nova-rey/pisxme/pisxme/reva-clean/PHASE19_BLOCKER_REPORT.md

# Phase 19 SATA routing blocker (active, non-terminal)

## 2026-09-05 orthogonal coordinated-generator sweep

A direct-generator class evaluated U7 rotation 180 with explicit orthogonal
J3 launches at `(140,110)/(180,95)`, `(170,110)/(230,95)`, and
`(190,100)/(250,95)`. Native DRC measured `434`, `377`, and `416` violations;
each retained `413` unconnected items and `17`, `21`, and `24` crossing/short
records. Coordinate-only movement does not repair the stale route construction.
The next implementation must replace the bridge/socket route topology from
live pad coordinates while co-generating the clock network. No sweep candidate
is promoted.

## 2026-09-05 live U7 rotation-180 clock transform correction

The clock authoring path previously used the old synthetic U7 origin even when
applied to `PHASE19_COORDINATED_PASS_CANDIDATE_FINAL` (`U7` at `(120,140)`,
rotation 180). The generic fixture now reflects its passing local graph about
the live U7 center and supports a parameterized support shift. The generated
clock support is at the expected transformed locations (`Y1` `(120,125)`
before shift), and the three U7 clock routes land on serialized pads
`52=(123,135.5)`, `53=(122.5,135.5)`, and `54=(122,135.5)`.

The corrected no-shift candidate was rejected at 234 native DRC violations /
413 unconnected items, with new records where the correctly landed clock
routes occupy the inherited SATA corridor. A west-shifted run reduced the
clock-related crossing/short class to 10 records but still collided with
live SATA and regulator geometry. This closes the stale-coordinate hypothesis
and identifies the next required class: regenerate U7/J3/clock together with
the clock support outside the live SATA corridor.

The corrected live-U7 transform was swept with support shifts `-5, -10, -15,
-20, -25, -30, -35, -40 mm` on the best no-crossing coordinated ancestor.
The best result was the `-20 mm` shift at 245 native DRC violations / 417
unconnected items, with 9 crossing/short records; the other shifts were no
better. This bounded negative result confirms that moving clock support within
the existing U7/J3 placement cannot clear SATA occupancy. The next credible
step is one regenerated storage island with a dedicated clock corridor.

An outboard coordinated storage-room experiment moved U7 to `(180,140)` and
J3 to `(250,100)` while retaining the V3 SATA authoring branch, then applied
the corrected live-U7 clock transform with a `-20 mm` support shift. Native
DRC reported `417` unconnected items and 29 crossing/short records. The
candidate is rejected: the outboard J3 move alone does not repair the stale
USB3/SATA route construction or provide a valid integrated clock corridor.
No PCIe or architecture change was made.

An occupancy-aware routing experiment was then added as a bounded diagnostic.
It derives the live U7 clock pads, places the oscillator island in open
acreage, and routes each clock net on B.Cu while treating inherited copper and
previously emitted nets as obstacles. The source-to-crystal search exposes a
closed inherited B.Cu corridor at the proposed support field before a complete
passive branch can be emitted. The experiment is retained as rejected
evidence; it does not weaken the layer contract or validate a partial clock
network. The next credible implementation must move the complete U7/J3
storage island, not just the support footprints, so the clock and SATA
corridors are planned together.

## 2026-09-04 local underside clock-island follow-up

The next authorized class was implemented as a parameterized authoring path in
`phase19_clock_local_bcu.py`. It keeps the authoritative U7 XI/VSSOSC/XO
escape perpendicular at the live rot270 pad row, transitions with ordinary
through-vias, and places the low-profile Y1/R23/C42/C43 support island on
B.Cu. This removes the earlier F.Cu clock trunk through the inherited USB3
and low-speed corridors.

The first corrected run exposed two further facts. The inherited coordinated
candidate contains substantial pre-existing connectivity/clearance debt, and
the underside support graph must be routed as a planar perimeter rather than
as a three-net star. The near-support run (`Y1` at `(145,125)`) measured 365
native DRC violations / 429 unconnected items and still has clock-local
XI/XO/VSSOSC crossings at the support field. A south-acreage run (`Y1` at
`(140,160)`) measured 366 / 429 and has the same local support-field class.
The experiments are rejected; no Phase 19 gate is claimed closed.

The U7-side failure is now correctly separated from the previous error: the
first version routed vertically through adjacent no-connect QFN pads 50/51;
the generic path was corrected to leave the 0.5 mm pitch row laterally first.
The remaining blocker is the support-island topology and available copper
corridor, not a missing TUSB9261 clock authority. The passing isolated clock
fixture remains the electrical reference. PCIe, USB3/SATA architecture,
stack, and Phase 18 ancestor are unchanged.

The required independent Consultant unblocker review was invoked with the
current Phase 18 ancestor, Phase 19 report, exact U7/J3 coordinates, and the
failed underside trials. The session exceeded the bounded response window
and was cancelled; this is recorded as orchestration latency, not evidence of
an engineering hard block. The selected continuation remains in-scope:
author a planar oscillator perimeter with explicit live pad coordinates,
co-locate it during the rotated U7/J3 generation, and validate the clock delta
against the SATA-only ancestor before any promotion.

A second placement sweep moved the underside support island to upper-right and
lower-edge acreage (`Y1` at `(200,100)`, `(220,100)`, `(250,90)`, and
`(260,160)`). Native DRC remained in the `364--375` violation range with
`429` unconnected items; clock-local support-field crossings/shorts remained,
and some placements additionally intersected inherited CM5/PCIe/connector
copper. No placement was promoted. The next authoring change must use the
known passing isolated-clock graph as the local support template and
regenerate its three U7 source corridors together, rather than applying
another support-coordinate-only overlay.

The coordinated generator was also exercised directly at U7/J3 placements
`(150,100)/(230,100)`, `(180,90)/(250,105)`, and `(200,80)/(270,100)` with
the authoritative V3 SATA branch and U7 rotation 180. Native DRC measured
`426`, `473`, and `364` violations respectively, with `413` unconnected
items in each artifact and `13`, `20`, and `24` crossing/short records. These
are rejected as placement sweep evidence: the lower raw DRC count does not
pass because the coordinated USB3/SATA connectivity gate remains open, and
the clock network still has to be generated and routed as part of the same
candidate.

## 2026-09-04 coordinated storage authoring repair

The coordinated-island generator was corrected after a KiCad 10 serialization
audit. The Phase 18 donor reuses C30-C33 for unrelated regulator capacitors;
the generator now removes those donor footprints and loads the project-local
0402 footprints. It also assigns explicit net codes and attaches the new
socket-side nets before synchronization reload, preserving the intended
C30-C33/J3 split mapping.

Disposable candidate U7 `(150,140)` / J3 `(180,125)` completed generation and
serialized the expected four SATA socket nets, but native DRC measured 262
violations. Candidate-introduced SATA launch crossings/shorts and inherited
CM5/PERST interactions remain, so this candidate is rejected. Evidence is in
`PHASE19_COORDINATED_STORAGE_REPAIR_RECEIPT.md`; Phase 19 remains active and
no Phase 20+ work has started.

Follow-up USB3 escape refinement reduced the USB-only V3 disposable report to
200 native DRC violations by approaching the moved U7 row horizontally, but
it still crosses inherited CM5/PCIe source-corridor geometry and is rejected.
This remains a coordinated storage-island routing experiment, not a Phase 19
closure claim.

The best current coordinated V3 run (`PHASE19_BEST.kicad_pcb`, U7 `(120,140)`
180 degrees, J3 `(145,125)` 90 degrees) measured 206 native DRC violations.
It retains one J3 auxiliary-pad short and two USB3/PCIe or local corridor
crossings, so it is rejected. The cap-net serialization failures remain fixed.

The refined synchronized candidate `PHASE19_LIVE3.kicad_pcb` is the current
best local result: native DRC measured 207 violations with zero shorting-item
records and one remaining USB3 source/landing crossing. It also retains
inherited clearance/hole/unconnected debt, so Phase 19 remains open and the
candidate is rejected.

Date: 2026-09-04

Status: `PISXME_REVA_CLEAN_PHASE19_SATA_ROUTING_IN_PROGRESS`

## 2026-09-04 coordinated-island continuation

The authoring harness was corrected so C30-C33 follow the requested U7
coordinate instead of retaining the former fixed x positions. A second
correction adds an opt-in direct USB3 landing mode for the validated
Phase-18 U7 neighborhood. With U7 `(110,105)` and USB3-only generation,
native DRC reports zero USB3 `tracks_crossing` and zero USB3 `shorting_items`;
the one remaining crossing/short category is inherited CM5/PERST or frozen
PCIe geometry outside the USB3 island.

The first complete orthogonal SATA launch experiment at U7 `(110,105)` and
J3 `(150,110)` rotation 0 was rejected. Native DRC identified concrete local
failures: RX_N crossing the frozen PCIe B.Cu corridor, connector-pad launch
shorts caused by the trial's J3 approach points, and one RX via near an
existing power-input pad. This is evidence against that exact trial, not
against the CM5-to-SATA architecture. No PCIe or Phase-18 ancestor copper was
modified.

The active blocker therefore remains a recoverable coordinated storage-island
placement/routing problem. The next bounded experiment must move the complete
island into genuinely open acreage or adjust the J3 orientation/edge while
retaining the direct USB3 landing mode, then derive all SATA launch points
from the actual connector pad and courtyard geometry. Phase 19 remains open;
Phase 20+ has not started.

## Independent high-speed review and V3-cap continuation

An independent PCB review confirmed the prior crossing diagnosis: the named
`(95,140)` marker is the RX_N landing segment, and its actual conflict is the
F.Cu TX_N diagonal, not TX_P. The review also identified that the direct
RX_N patch must account for the adjacent U7 pad field and that the live
candidate is not SI-closed until length/skew and transition-return evidence
are measured.

The generator now has an opt-in `P19_RXN_DIRECT` branch that preserves the
source corridor and uses a short ordinary-via return beside the serialized
RX_N pad. A V3-cap candidate using U7 `(120,140)` rotation 180 and J3
`(145,125)` rotation 90, with C30-C33 placed inline in the proven V3 lanes,
was generated and reloaded by KiCad 10. Native DRC measured 316 total
violations, zero `shorting_items`, and one `tracks_crossing`. The sole
crossing is RX_N on B.Cu against the frozen PCIe B.Cu trunk; SATA itself has
zero crossing/short records in this candidate. It is therefore rejected but
is the best current decomposition of the remaining problem.

The next experiment must move that one RX_N transition off the PCIe trunk or
select a nearby U7/J3 placement with the same V3 SATA lane ordering. It must
also include the independent review's required USB3 pair-length/skew audit
and local GND return-via review. A separate review noted U7 clock pads 52/53
remain unassigned in the current inherited materialization; this is retained
as a Phase 7/19 authority item and is not silently waived.

## 2026-09-04 coordinated repath baseline

The coordinated USB3 repath was extended across all four branches while
retaining the V3 split-cap SATA geometry. The generated/reloaded candidate is
`PHASE19_COORDINATED_PASS_CANDIDATE3.kicad_pcb` with U7 `(120,140)` rotation
180 and J3 `(145,125)` rotation 90. Native DRC reports 189 total violations,
418 unconnected items, zero `tracks_crossing`, zero `shorting_items`, and the
three inherited clearance plus two inherited hole-clearance records, with the
same five inherited dangling-via records as the accepted Phase-18 acreage
baseline. No candidate-introduced true clearance, short, or crossing remains
in the high-speed routing categories.

The candidate also removes the inherited duplicate U7 pad-net records on
pads 5-12 in the serialized output. The authoritative mapped pads remain:
USB3 42/43/45/46 and SATA 57/56/60/59. Native reload confirms two endpoint
pads and routed copper for each of the four USB3 nets, each of the four
bridge-side SATA nets, and each of the four socket-side SATA nets; no
high-speed unconnected-item records remain after the stale records are
removed.

The first path-length audit is not yet acceptable for SI closure. Summed
copper lengths are USB3 RX_N 108.473 mm, RX_P 87.104 mm, TX_N 81.453 mm, and
TX_P 61.407 mm; SATA full-path copper sums across bridge and socket sides are
TX_P 24.856 mm, TX_N 80.225 mm, RX_P 48.975 mm, and RX_N 59.775 mm including
the split-cap corridors. These are
candidate measurements, not a claim of compliance. The next repair must add
controlled, pair-symmetric length tuning without reintroducing crossings,
forbidden-layer signals, pad-field violations, or unnecessary transitions.

## Current evidence

### 2026-09-04 continuation: SATA coupling network implemented

The earlier missing-implementation finding has been corrected generically in
`phase7_storage.py` and checkpointed at `db574ab`. Native KiCad 10 child-netlist
export now proves four separate paths:

| Bridge-side | Part | Socket-side |
| --- | --- | --- |
| `BRIDGE_SATA_TX_P` | C30 `GRM155R71C104KA88D`, 100 nF, 0402 | `SATA_M2_TX_P` → J3 pad 1 |
| `BRIDGE_SATA_TX_N` | C31 `GRM155R71C104KA88D`, 100 nF, 0402 | `SATA_M2_TX_N` → J3 pad 2 |
| `BRIDGE_SATA_RX_P` | C32 `GRM155R71C104KA88D`, 100 nF, 0402 | `SATA_M2_RX_P` → J3 pad 3 |
| `BRIDGE_SATA_RX_N` | C33 `GRM155R71C104KA88D`, 100 nF, 0402 | `SATA_M2_RX_N` → J3 pad 4 |

The PCB materializer loads four matching footprints and native DRC confirms
they are represented as physical pads. This closes the schematic/netlist
implementation gap, but not the Phase 19 routing gate: the coordinated PCB
generator still needs to route both sides of every capacitor and then prove
the full U7→C30-C33→J3 channel.

The closed Phase 18 CM5-to-U7 USB3 route remains valid at U7 `(110,105)`.
The coordinated moved-U7 experiment was rejected because regenerated USB3
escapes crossed the frozen PCIe field and U7 support pads. The J3-only trial
was also rejected: the selected rotated M.2 endpoint arrangement interleaved
the SATA groups with the fixed U7 launch and existing copper.

Native KiCad 10 DRC receipts:

| Candidate | Result | New failure class |
| --- | ---: | --- |
| `ACREAGE_PHASE19_STORAGE_MIDACREAGE_COORDINATED.kicad_pcb` | 232 violations / 426 unconnected | USB3/SATA endpoint crossings and pad-field shorts; inherited baseline separate |
| `ACREAGE_PHASE19_SATA_J3_ONLY.kicad_pcb` | 234 violations / 426 unconnected | J3 launch/endpoint crossings and shorts; inherited baseline separate |
| `ACREAGE_PHASE19_SATA_OUTBOARD_MONOTONIC.kicad_pcb` | 246 violations / 426 unconnected | fixed-board PCIe/reference intersections plus M.2 launch crossings; inherited baseline separate |
| `ACREAGE_PHASE19_SATA_UNDERSIDE_ENDPOINT.kicad_pcb` | 243 violations / 430 unconnected | TX source/connector crossings, one frozen PCIe B.Cu intersection, and connector-hole clearance; inherited baseline separate |
| `ACREAGE_PHASE19_SATA_LOCAL_UNDERSIDE.kicad_pcb` | 244 violations / 430 unconnected | U7 pad-field conflicts, two local B.Cu pair crossings, and M.2 courtyard/clearance interactions; inherited baseline separate |
| `ACREAGE_PHASE19_STORAGE_MIDACREAGE_SATA_LAUNCH_V3.kicad_pcb` | 198 violations / 430 unconnected | no new short/crossing category; SATA-only proof, not coordinated-board closure |
| `ACREAGE_PHASE19_STORAGE_COORDINATED_FRESH.kicad_pcb` | 208 violations / 426 unconnected | regenerated USB3 source/landing crossings and local PERST/USB3 interactions; SATA V3 corridor retained |

The V3 result is useful evidence for a local SATA corridor, but is not
promoted because its moved U7 leaves the already-closed USB3 route stale.

The outboard trial kept U7 and USB3 unchanged and moved J3 to `(180,125)` at
rotation 0°. It still introduced crossings against the fixed reference field
and connector launch geometry, so it is rejected rather than treated as a
passing long detour.

The underside trial kept the same U7/USB3 ancestor and placed J3 on B.Cu at
`(180,125)`, rotation 0°. It reduced the top-side obstruction but its current
split-layer source/connector escape still crosses the frozen B.Cu field and
violates connector-hole clearance, so it is also rejected.

## Next authorized continuation

Keep U7 and the Phase 18 USB3 route frozen. Continue with a bounded M.2
endpoint placement/orientation search, using the proven SATA V3 escape as the
starting geometry. Candidates must pass focused native DRC for all four SATA
nets, preserve 100-ohm ordinary F.Cu/B.Cu routing, and avoid plane-layer
signals, stubs, shorts, crossings, and connector/mechanical conflicts.

Phase 20+ has not started. The authorized local endpoint/underside classes are
now exhausted. The user has explicitly authorized reopening the coherent U7/J3
storage island, including regeneration of both USB3 and SATA routing. The fresh
coordinated candidate at U7 `(120,140)` / J3 `(145,125)` is rejected as an
experiment, but demonstrates that the remaining failure is local USB3 landing
geometry rather than a reason to preserve the former U7 coordinate. Phase 19
remains active; further co-located island candidates will keep the PCIe
ancestor unchanged.

Generator-correction experiment: the USB3 source-side escapes were restored
to the validated Phase 18 geometry and the moved-U7 landing was made
coordinate-derived. An above-PCIe placement at U7 `(140,100)` / J3 `(180,90)`
was rejected by native DRC at 410 violations / 426 unconnected, including
PCIe interactions and local SATA shorts. This class is not promoted; the next
search remains in open acreage beside/below the validated PCIe corridor.

Placement-sweep continuation: U7/J3 `(140,140)/(170,125)` was the best
tested open-acreage class at 224 violations / 426 unconnected, but retained
real USB3/PERST and pair crossings. A coordinate-derived SATA-lane refinement
measured 229 / 426 and introduced local SATA lane crossings/shorts; it is
rejected. No PCIe geometry changed.

Native synchronization correction: after moving U7/J3, the generator now
serializes and reloads the board before reading transformed pad coordinates.
The corrected U7 `(140,130)` / J3 `(180,115)` candidate measured 227 native
DRC violations / 426 unconnected before SATA escape refinement; the next
escape refinement measured 229 / 426 and reintroduced SATA/USB3 crossings.
Both are rejected experiments. This closes the stale-pad-coordinate defect
in the experiment harness, not Phase 19.

Staged USB3 rail experiment: kept the synchronized U7 `(140,130)` / J3
`(180,115)` placement and moved each final vertical transition onto B.Cu
after an F.Cu staging hop. Native DRC remained 229 violations / 426
unconnected and reported new SATA/USB3 pair interactions; rejected. The next
continuation changes island orientation/relative placement rather than adding
another same-geometry rail variant.

Cross-class coordinated trial: used the SATA V3 candidate as the input board
and regenerated USB3 after the native pad-coordinate synchronization fix.
`ACREAGE_PHASE19_STORAGE_V3_USB_REGEN.kicad_pcb` measured 226 native DRC
violations / 426 unconnected, with SATA/USB3 crossings and pad-field
interactions. Rejected; the SATA V3 geometry cannot simply be combined with
the regenerated USB3 path.

Orientation sweep continuation: U7/J3 rotations at `(150,140)/(190,140)`
and `(145,135)/(190,135)` measured 277/415 and 265/408 native DRC
violations respectively. Rotation-only classes are rejected; the coupled
U7 pad-field escape remains the active engineering issue.

Direct-F.Cu USB3 isolation trial: with SATA tracks removed from the corrected
U7 `(140,130)` candidate, native DRC measured 211 violations / 430
unconnected. Three candidate-introduced failures were shorts against the
regulator support island and one crossing against the frozen PCIe B.Cu field.
This identifies the next local repair target; no PCIe architecture change is
implied.

Exact-source USB3 follow-up: preserving the Phase 18 CM5 escape layering and
using a direct local F.Cu detour to U7 `(140,130)` reduced the isolated USB3
candidate to 202 violations / 430 unconnected, with no new USB3 short or
crossing category. The complete east-edge SATA trial at J3 `(240,140)` was
then rejected at 228 violations / 426 unconnected because its SATA launch
still crosses/shorts at the connector and U7 field. Phase 19 remains active.

Specialist-recommended orientation trial: U7 `(170,140)`, rotation `90°`,
with J3 `(205,120)`, rotation `90°`, was implemented with an orientation-aware
horizontal USB pad-row escape. Native DRC measured 378 violations / 426
unconnected and was rejected. The recommendation remains useful: its
placement clears the C19/PERST area, but the current SATA launch and remaining
local support interactions require another coordinated route.

Valid reuse check: SATA regeneration was disabled and only USB3 was reauthored
on the existing V3 SATA board. The resulting candidate measured 242 native DRC
violations / 426 unconnected and retained four USB3 short/crossing findings
against preserved V3 copper. Simple overlay reuse is rejected; a fresh
coordinated route remains required.

The TI implementation-guide review also found an open implementation gap:
four inline SATA AC-coupling capacitors (one per conductor, 0402 or smaller,
symmetrically close to J3; no C-pack) are absent from `STORAGE.kicad_sch`.
This is recorded in `PHASE19_SATA_AC_CAP_RECEIPT.md`. Phase 19 cannot close
until the authoritative schematic/netlist and routed capacitor network exist.

Transform audit: the unblocker-recommended U7 `(120,140)` `90°` candidate
was serialized and inspected. KiCad 10 actually places its USB row at
`y=135.5` and SATA row at `x=124.5`; the earlier predicted transform was
mirrored. The bottom-approach branch therefore entered the U7 body and
measured 219 USB-only DRC violations / 430 unconnected. It is rejected;
subsequent routing must use serialized pad coordinates directly.

Regulator-support reopening: translating only C18/C19 to `(100,145)/(108,145)`
on the U7 `(140,130)` USB3 isolation candidate removed the three prior
`BRIDGE_3V3` shorts. Native DRC remained 202 violations / 430 unconnected,
matching the Phase 18 baseline class apart from one local clearance. This
confirms the authorized coherent support move is electrically safe in the
disposable proof; complete Phase 19 remains gated by SATA launch geometry.

## 2026-09-04 clock-pin authority audit

The independent review's reference to U7 pads 52/53 was checked against the
local TI implementation-guide and Rev-I datasheet records. The exact PVP
pinout is: pin 52 `XI`, pin 54 `XO`, and pin 53 `VSSOSC`; these are not an
unassigned SATA or USB pair. TI's implementation guide requires a 40 MHz
reference, either a crystal between XI/XO or an external clock on XI with XO
left open, and a local VSSOSC return. The current abstract twelve-pin storage
symbol and clean schematic expose neither the oscillator network nor these
three pins. This is a genuine pre-release storage-authority gap discovered
during Phase 19, not a reason to waive the routing gate. It must be corrected
in the storage authoring path and then included in the coordinated PCB/SI
revalidation before Phase 19 can close.

The stable V3-cap generator branch was cleaned of the rejected tuned-cap
variant and re-run at U7 `(120,140)` / J3 `(145,125)`, U7 rotation 180° and
J3 rotation 90°. Native KiCad DRC again measured 189 total violations / 413
unconnected items, with zero `tracks_crossing` and zero `shorting_items`.
The candidate is retained as the best geometric baseline, but remains
`REJECTED_EXPERIMENT` because USB3 and SATA full-path length balance,
transition-return evidence, and the newly confirmed 40 MHz clock network are
not closed.

## 2026-09-04 hierarchy/materialization correction and clock-network proof

The storage authoring path was corrected generically. The failure was not a
missing KiCad project-instance path: the newly added clock library symbols had
been emitted after the STORAGE library closure and were therefore malformed
top-level symbols. The repair now places them inside the child `lib_symbols`
section and rebuilds their instances idempotently. Native KiCad 10 root export
now includes U7, J3, Y1, R23, C42, and C43.

The root netlist proof now shows:

* U7.30 and U7.31 on `/STORAGE/BRIDGE_3V3`;
* U7.52/XI, Y1.1, R23.1, and C42.1 on `/STORAGE/BRIDGE_XI`;
* U7.54/XO, Y1.3, R23.2, and C43.1 on `/STORAGE/BRIDGE_XO`;
* U7.53/VSSOSC, Y1.2/Y1.4, C42.2, and C43.2 on the distinct
  `/STORAGE/BRIDGE_VSSOSC` net.

The corrected materializer reload proof assigns those exact nets to the
physical U7 and clock-support pads and materializes 74 components, 238 nets,
and six copper layers. The clock island follows U7 in the coordinated
candidate; Y1 has its two electrical pads plus two VSSOSC return pads, with no
via-in-pad. This removes the prior SATA/VSSOSC alias and is now a valid
authoring/materialization baseline.

Phase 19 is still active. The coordinated routed candidate has not yet been
promoted: it still requires the short physical XI/XO/VSSOSC copper loop,
clock-to-high-speed clearance review, and the outstanding USB3/SATA
length/reference/return-via acceptance evidence. The candidate remains
`REJECTED_EXPERIMENT` pending those checks; no Phase 20 work has started.

## 2026-09-04 clock-loop routing experiment

A disposable physical clock-island experiment was applied to the best
coordinated SATA/USB3 candidate. It carried U7.30/U7.31, U7.52/U7.53/U7.54,
Y1, R23, C42, and C43 with the corrected net assignments. The first direct
F.Cu star/branch loop was rejected: native KiCad DRC measured 212 violations
and 415 unconnected items, including new `tracks_crossing` and
`shorting_items` records between XI, XO, and VSSOSC. The experiment is not
evidence against the crystal architecture; it is a failed local escape class.

The valid retained state is the schematic/netlist/materialization baseline,
not this routed experiment. Further work must use an ordinary-via,
layer-separated short clock escape with the exact pad coordinates, then
re-run focused native DRC and return/reference checks before promotion.

A second disposable class placed Y1/R23/C42/C43 on the underside and used
ordinary F.Cu-to-B.Cu transitions from the U7 clock pads. It was also rejected:
native KiCad DRC measured 249 violations and 428 unconnected items, with new
clock/high-speed `tracks_crossing` and `shorting_items` records. The underside
is permitted by the Rev-A mechanical contract, but this particular transition
geometry is not acceptable. The next experiment must change the local U7 clock
escape/placement relationship, not relax the layer policy or reuse either
failed clock route.

## 2026-09-04 open-side clock corridor experiment

The next disposable class used the materialized U7 at `(250,105)` and moved
the existing authoritative Y1/R23/C42/C43 footprints into the genuinely open
east-side acreage around `(255..261,112..118)`. The experiment used native
KiCad-reported transformed pad coordinates rather than assumed footprint-local
coordinates, assigned the exact XI/XO/VSSOSC nets, and kept VSSOSC distinct
from board GND. It measured 271 native DRC violations / 475 unconnected items,
versus 206 / 484 for its inherited materialization baseline.

This class is rejected. The new records are concrete clock-fanout failures:
the three adjacent U7 clock pads need a monotonic escape before they can branch
to the crystal and load capacitors; the attempted same-side branches crossed
one another and the VSSOSC return. The FREQSEL fanout also approached an
unassigned neighboring pad. This is not evidence against the required crystal
mode or against the open-side placement; it identifies the next necessary
experiment as a pad-row escape/rotation change with one net per corridor,
followed by a fresh coordinated USB3/SATA candidate. No Phase 19 gate was
relaxed and no Phase 20 work started.

## 2026-09-04 consultant review and perpendicular-first follow-up

The independent consultant reviewed the three rejected clock classes and the
current materialized geometry. It identified a common topology defect rather
than a placement or architecture defect: each prior trial ran at least one
clock track along the 0.5 mm-pitch U7 pad row before turning away. The exact
U7 row is 52/XI `(247.0,109.5)`, 53/VSSOSC `(247.5,109.5)`, 54/XO
`(248.0,109.5)`, with adjacent no-net pads 51 and 55. It also found that the
trial helper used 0.15 mm traces against a 0.20 mm board minimum.

The consultant recommended retaining the open east-side support placement,
escaping each clock pad perpendicular to the row before any lateral turn, and
using separated corridors for the subsequent crystal branches. This is an
in-scope authoring/routing correction. It does not require changing the
TUSB9261 clock architecture, layer contract, or PCIe corridor.

The follow-up applied the perpendicular-first breakout and raised the trial
trace width to 0.20 mm. Native KiCad DRC improved to 225 violations / 474
unconnected items, but the trial still generated clock-only crossings and
shorts in the downstream same-layer XI/XO/VSSOSC branches. It is rejected;
the result confirms the U7-row defect was real but that the crystal-side
branch topology must also be changed. Phase 19 remains active and Phase 20+
remain untouched.

## 2026-09-04 minimal clock fixture continuation

To separate clock topology from the inherited acreage debt, a disposable native
KiCad fixture retained the real TUSB9261 footprint and Y1/R23/C42/C43 while
removing unrelated footprints, copper, and zones. The fixture used a
perpendicular-first U7 escape, an ordinary through-via VSSOSC return, and
separate F.Cu/B.Cu corridors. Native KiCad DRC measured 15 violations / 2
unconnected items, with no `shorting_items` records. The remaining clock
records are two same-side escape crossings, one local clearance violation,
and one dangling VSSOSC bus endpoint; the two unconnected items are the
fixture's intentionally isolated U7.30/U7.31/BRIDGE_3V3 tie.

This is the best current clock topology experiment but is not yet closed: the
two escape crossings must be removed and the 3V3 frequency-select tie must be
made explicit in the fixture before applying the clock route to the complete
coordinated storage island. The result confirms that the clock network is
implementable with the approved architecture and layers; Phase 19 remains
active and Phase 20+ remain untouched.

## 2026-09-04 acreage clock integration baseline

The cleaned minimal clock topology was applied with a relative transform to
the materialized acreage candidate, preserving U7 and moving only the local
clock support island. The integration harness removes any inherited clock-net
tracks before adding the corrected route, and compensates dynamic pad
coordinates so no stale transformed endpoint is serialized. Native KiCad DRC
measured 207 violations / 473 unconnected items versus 206 violations for the
materialization baseline. The report contains no new clock `tracks_crossing`,
`shorting_items`, or runaway-length VSSOSC records; the remaining DRC debt is
inherited board geometry and incomplete non-clock routing.

This is a usable clock integration baseline, not Phase 19 closure. The next
step is to apply the same relative clock island to the complete coordinated
USB3/SATA candidate and rerun the full storage SI, return-via, and native DRC
gates. Phase 20+ remain untouched.

## 2026-09-04 clean minimal clock fixture and coordinated transplant

The minimal fixture was refined to close the explicit FREQSEL0/FREQSEL1 tie
and terminate the VSSOSC return at a connected ordinary-via bus. Native KiCad
DRC reports 12 warnings, zero unconnected pads, zero clock shorts, and zero
clock crossings; the remaining warnings are silkscreen/copper-sliver checks.
This closes the clock topology as a disposable electrical fixture, not as an
acreage release artifact.

The same relative geometry was then applied to the coordinated storage
candidate at U7 `(140,110)` / J3 `(145,125)`, with inherited clock copper
removed before routing. That transplant was rejected at 406 violations / 471
unconnected items because the candidate's live SATA/USB3 copper occupies the
translated support corridors and the new clock branches collide with those
signals. The result is a valid rejection of this placement transplant, not of
the clean minimal topology. The next experiment must relocate the complete
clock support island into a corridor clear of the already-routed USB3/SATA
fields, then regenerate the coordinated candidate. Phase 19 remains active;
Phase 20+ remain untouched.

## 2026-09-04 coordinated live-copper occupancy map

The coordinated candidate was inspected with native `pcbnew` geometry rather
than relying on footprint courtyards alone. Around U7 `(140,110)`, rotation
180 degrees, the clock row is top-facing: 52/XI `(143.0,105.5)`, 53/VSSOSC
`(142.5,105.5)`, and 54/XO `(142.0,105.5)`. The active F.Cu storage field
contains the SATA bridge launches at x=`139.0..141.0`, the SATA socket
approaches at x=`134.5..136.5`, and the USB3/PCIe source corridors extend
through the same local field. B.Cu contains the SATA RX continuation near
y=`130..138`, leaving only a narrow upper/left B.Cu window for a clock
transition and local support island.

This map explains both fixed-offset transplant failures: the nominal north
and east locations were not free once live copper and pad fields were
considered. The next disposable candidate will use a deliberate
perpendicular F.Cu escape from the top-facing U7 clock row, transition only
after the row is clear, and place the low-profile clock support in the mapped
B.Cu window. No validated USB3/SATA/PCIe copper will be overwritten, and no
Phase 19 closure claim is made yet.

## 2026-09-04 rotated north-corridor transplant rejection

The clean minimal clock route was reflected for the coordinated U7 rotation
and moved the support island north/outboard of U7, with the clock-net tracks
removed before regeneration. The coordinated candidate's live copper map
shows SATA launch and USB3/PCIe corridors in the apparently open north region;
native KiCad DRC measured 509 violations / 471 unconnected items, including
new clock-to-storage/power crossings and shorts. This candidate is rejected.

The result closes the fixed-offset transplant class: a clean isolated clock
fixture cannot be promoted by geometric reflection alone when the coordinated
candidate contains active high-speed copper. The next candidate must use a
live-copper occupancy map to place the clock island in a genuinely empty
acreage corridor, then route the short clock loop before full SI review. No
architecture, layer, or PCIe gate was relaxed; Phase 19 remains active and
Phase 20+ remain untouched.
## 2026-09-04 mapped B.Cu clock-island rejection

The live-copper map was used to build a disposable coordinated candidate with
U7's top-facing clock row escaping on F.Cu and Y1/R23/C42/C43 placed on B.Cu
in the measured west window. The clock-net copper was removed before the
trial, all clock pads were assigned explicitly, and the U7 FREQSEL pins were
tied to the bridge 3.3 V rail. Native KiCad DRC measured 386 violations / 477
unconnected items, including new clock-to-live-storage crossings and shorts.

The mapped window is rejected as insufficient once the complete candidate's
pad fields and B.Cu storage transitions are included. The clean minimal clock
fixture remains electrically closed; this is a placement/corridor failure.
The next experiment must move the low-profile clock support farther from the
U7/SATA pad field and route the three clock nets with a local layer-separated
escape, using the live occupancy map at each proposed coordinate. Phase 19
remains active; Phase 20+ remain untouched.

## 2026-09-04 south-acreage clock corridor audit

The live coordinated candidate was re-audited against the explicit Rev-A
mechanical contract. The board outline is approximately `300 x 180 mm`; live
storage copper is concentrated above about `y=140 mm`, and the prior generic
V100 cooler/backplate exclusion is not a Rev-A constraint. This leaves a real
south-acreage corridor for low-profile bridge-clock support. No PCIe, CM5,
SXM2, connector, standoff, M.2, or enclosure-floor authority currently blocks
that region.

A disposable south-corridor transplant placed Y1/R23/C42/C43 at `(220,150)`,
`(230,150)`, `(220,160)`, and `(230,160)`. Native KiCad DRC reported `407`
violations and `466` unconnected items. Inspection found that the new clock
errors were caused by the experiment authoring itself: support branches were
serialized to non-pad coordinates, the VSSOSC lane intersected an existing
power pad near `(159.35,150)`, and local XO/VSSOSC branches crossed at the Y1
field. Existing SATA/USB3 errors were also present.

This candidate is rejected as invalid proof, not evidence against the south
corridor. The corrected continuation must use exact reloaded pad coordinates
for every support endpoint, put all long clock lanes outside the live
high-speed envelope before descending, and preserve the passing
minimal-fixture topology. Phase 19 remains active; Phase 20+ remains
untouched.

## 2026-09-05 opposite-side coupling/socket trial

Following the consultant recommendation, the disposable moved U7 to
`(260,105)` rotation `270`, placed C30-C33 on its west side, and moved J3 to
`(200,140)` rotation `90`, putting the coupling-to-socket travel on the side
opposite the bridge package. The stale M.2 mechanical donor keepout was
removed, and USB3, SATA, and the 40-MHz clock were regenerated together from
the prepared KiCad board.

Native DRC measured `377` violations and `476` unconnected items. This is the
best raw result of the consultant-directed placement class, but it is still
rejected: the live SATA launch remains entangled with the U7/regulator pad
field and the clock fanout still has layer crossings. No production clean
artifact, PCIe route, or architecture was changed. Phase 19 remains open;
Phase 20+ has not started.

## 2026-09-04 coordinated U7 rotation-270 trial

The generator invocation path was corrected and used to produce a distinct
coordinated candidate with U7 at `(140,130)`, rotation `270` degrees, and J3
at `(180,115)`. This is the first complete candidate in the new orientation;
the U7 clock row is on the west side while the SATA pins remain on the
opposite local side. The USB3/SATA island was regenerated from the Phase 18
ancestor without modifying PCIe.

After adding the authoritative 40 MHz clock network and the south support
island, native KiCad DRC measured `486` violations and `416` unconnected
items. The candidate is rejected. New records show that the generated SATA
launch still occupies the local U7 pad-row escape, and the trial's ordinary
clock vias also encounter inherited unfilled-plane/zone rule records. This is
not evidence against rotation 270: it identifies the required next repair as
clock-aware SATA pad-row generation plus a native zone-fill/reload pass.
Phase 19 remains active; Phase 20+ remains untouched.

## 2026-09-04 U7 rotation-270 pad-field discriminating fixture

To distinguish a local U7 package impossibility from a coordinated-route
problem, a minimal native fixture retained only U7 in the rotation-270
orientation and assigned the three clock nets plus all four bridge-side SATA
nets. Clock pads 52/53/54 escaped west on F.Cu; SATA pads 56/57/59/60 escaped
east, with alternating permitted layers.

Native KiCad DRC reported `7` warnings and `5` unconnected items, with zero
`tracks_crossing` and zero `shorting_items` records. The warnings are the
intentional dangling ends of the isolated escapes; the five unconnected items
are unrelated inherited U7 support-pin pairs plus the two SATA B.Cu escapes
without connector endpoints. This fixture therefore proves that the rot270
U7 clock/SATA pad-field escape is geometrically legal. The remaining failure
is the coordinated SATA launch authoring, which must be regenerated around
the proven clock escape. Phase 19 remains active.

## 2026-09-04 rotation-270 candidate artifact and native crash repair

The previously missing rotated candidate was generated successfully after
isolating a KiCad 10 Flatpak SWIG crash in the coordinated generator. The
crash occurred while enumerating zones after footprint/net mutation; the
generator now makes zone refill opt-in for disposable candidates so the board
can be saved and reopened for native validation. The resulting artifact is
`PHASE19_COORDINATED_U7ROT270_FULL.kicad_pcb`, with native DRC `403` / `413`
before clock integration and `PHASE19_COORDINATED_U7ROT270_CLOCK.kicad_pcb`
with `486` / `416` after the first clock overlay.

The rot270 orientation remains the best geometric lead because the clock row
escapes west while the SATA pins face the other side. The first overlay is
rejected; its new errors are identifiable clock/SATA local escape crossings,
non-planar support fanout, and inherited zone/via-rule records. No Phase 19
closure claim is made.

## 2026-09-04 coordinated-generator invocation correction

The coordinated storage generator previously depended on host-side `P19_*`
environment overrides. Under the installed KiCad Flatpak those overrides were
not reliably visible, so a requested rotated-U7 candidate could not be
verified as a distinct artifact. The authoring path now accepts explicit
`--P19_NAME=value` arguments before importing `pcbnew`, preserving the same
parameter names while making native candidate generation deterministic.

No rotated-U7 candidate is promoted from the failed invocation. Phase 19
remains active pending a separately identified generated board and its native
USB3/SATA/clock validation.

## 2026-09-04 ordered B.Cu clock-trunk trial

The next trial used three ordered B.Cu trunk lanes after short U7 escapes,
with XI/XO/VSSOSC assigned monotonically before the south support island.
Native KiCad DRC measured `391` violations and `466` unconnected items. This
was an improvement over the prior `417`-violation trial, but it still produced
new clock errors because the U7-side transition was itself inside the active
SATA pad/launch field and the Y1 return dogbones were not planar with the
adjacent XI/XO pads.

The candidate is rejected. This closes the class of clock-only overlays on
the existing coordinated storage copper. The next in-scope repair must
regenerate the U7/J3 USB3/SATA island with clock-aware pad escapes as one
coherent candidate; the validated PCIe ancestor, layer contract, stack, and
storage architecture remain frozen.

## 2026-09-04 pre-field B.Cu trunk trial

A third south-corridor experiment moved the long XI/XO/VSSOSC trunks onto
separated ordinary-via B.Cu lanes before the J1/J3 fields. Native DRC measured
`391` violations and `466` unconnected items. This reduced the prior
F.Cu-through-field class, but the trial still introduced local clock
crossings: the three trunk lanes were not ordered monotonically through the
transition region, and the Y1 dogbones were still on the wrong side of the
adjacent return pads. It is rejected as a routing-topology experiment.

The result is still useful: the south support acreage does not itself collide
with the board's live copper. The remaining work is a planar, ordered B.Cu
escape plus exact local pad dogbones; no new component, architecture change,
PCIe reopening, or validation relaxation is indicated.

## 2026-09-04 corrected south-island clock trial

The south trial was corrected to use the exact serialized support-pad
coordinates and moved the support farther outboard to `(250,150)`, `(270,149)`,
`(250,170)`, and `(270,170)`. The proposed VSSOSC return was isolated on
B.Cu after an ordinary transition at `(200,92)`. Native DRC measured `417`
violations and `466` unconnected items.

The prior non-pad endpoint defect is gone. The remaining new records are
geometric: long F.Cu XI/XO trunks still enter the J3/J1 pad fields before
reaching the open acreage, and the adjacent Y1 clock-return dogbones need a
layer-separated pad escape. Existing SATA/USB3 debt remains inherited. The
candidate is rejected, but the result confirms the support area itself is
available. The next trial must transition the clock trunks before the J3/J1
fields and use a genuinely separate local return layer at Y1; no architecture,
PCIe, stack, or Phase 20 gate has been changed.

## 2026-09-04 clock control-fixture rerun

The native minimal TUSB9261 clock fixture was regenerated and checked again
after the south-corridor rejection. KiCad 10 DRC reports `12` warnings and
`0` unconnected pads; the report contains no `shorting_items` or
`tracks_crossing` records. The remaining warnings are non-electrical
silkscreen/text/copper-sliver checks. This reconfirms that the authoritative
40 MHz XI/XO/VSSOSC topology and perpendicular-first escape are implementable;
the unresolved issue is only integration into the fully routed acreage
candidate.

## 2026-09-04 rotation-aware SATA launch result

The generator now has an opt-in `P19_SATA_ROT270` branch. It places the
coupling capacitors for U7 rotation 270 and derives all bridge/socket launch
coordinates from reloaded transformed pads. The corrected SATA-only artifact
`PHASE19_COORDINATED_U7ROT270_SATAFIX.kicad_pcb` reports `340` native DRC
violations / `418` unconnected items, improving the prior rot270 artifact's
`403` / `413` result.

This is not a Phase 19 pass: the clock network has not yet been regenerated
against this corrected SATA ancestor, and the unconnected count remains open.
It is now the required ancestor for the next integrated clock trial.

## 2026-09-04 native footprint-rotation correction

The rotated minimal clock graph was rerun with KiCad's native footprint
rotation convention corrected from `90` to `270` degrees, and the support
island was shifted west of the corrected SATA ancestor. Native KiCad DRC
measured `388` violations and `420` unconnected items. The prior local
clock-support short class was removed; the remaining new records are west
clock-trunk crossings against the inherited USB3 corridor plus inherited
zone/via-rule debt.

This candidate is rejected as an integration candidate, but the correction is
retained in the generic clock fixture authoring path. The proven SATA ancestor
and isolated clock fixture remain valid; Phase 19 is still open.

## 2026-09-04 rotated minimal-topology transplant rejection

The passing minimal clock graph was rotated 90 degrees into the U7 rotation
270 coordinate system and applied to the corrected SATA ancestor. The support
footprints were rotated with the graph and the clock nets were created and
reloaded through the native authoring path. Native KiCad DRC measured `416`
violations and `424` unconnected items, including new local clock crossings
and XI/XO/VSSOSC shorts.

This rejects the transformed-support placement class, not the isolated clock
topology or the U7 rotation. The corrected SATA ancestor remains retained;
the next attempt must author a direct target-coordinate clock fanout around
the actual U7/J3/SATA fields rather than rely on a rigidly transformed graph.

## 2026-09-04 corrected-SATA clock-west integration trial

The authoritative clock network was rerun on the corrected
`PHASE19_COORDINATED_U7ROT270_SATAFIX.kicad_pcb` ancestor with a west/outboard
support island. Native KiCad DRC measured `372` violations and `423`
unconnected items, a material reduction from the prior rot270 clock-overlay
candidate (`486` / `416`). The trial is rejected because its local clock
fanout still crosses at the Y1 field and the inherited candidate retains
unconnected/shorting debt. The west-side SATA-aware ancestor remains the
correct basis; the next repair must replace the local clock fanout topology,
not revert the rotation-aware SATA launch.

## 2026-09-04 rotation-aware SATA launch generation

The coordinated generator was corrected so the `P19_SATA_V3` geometry is no
longer reused at U7 rotation 270. With U7 `(140,130)` rotation `270` and J3
`(180,115)` rotation `90`, the new opt-in `P19_SATA_ROT270` branch places the
four bridge-side coupling capacitors in an outboard local island and derives
all bridge/socket endpoints from reloaded transformed pads.

The corrected SATA-only coordinated artifact measured `340` native DRC
violations and `418` unconnected items, versus `403` and `413` for the prior
rot270 full candidate. The reduction confirms the former V3 coordinates were
an authoring defect, not a physical conclusion. The candidate is not
promoted: clock support has not yet been regenerated against the new
capacitor island, and the full USB3/SATA connectivity gate remains open.

## 2026-09-04 generalized rot270 storage-island trial

The rot270 SATA authoring branch was generalized to derive capacitor and launch
coordinates from the requested U7/J3 placement rather than absolute coordinates
from the first rot270 trial. A new coherent placement, U7 `(160,140)` rotation
`270` and J3 `(230,120)` rotation `90`, produced a SATA-only candidate at
`325` DRC violations / `418` unconnected items. Adding the transformed clock
network measured `371` / `420`, improving the prior rot270 integrated result
of `388` / `420`.

The candidate remains rejected because the transformed clock support still
crosses inherited USB3/low-speed corridors and the board-wide connectivity
gate is open. The result is retained as a valid generator/sweep data point;
PCIe, stack, layer contract, and storage architecture remain unchanged.

## 2026-09-04 west-shifted clock transform follow-up

The passing minimal clock graph was regenerated with native 270-degree support
footprint orientation and a westward support shift on the generalized
rot270-SATA candidate. Native KiCad DRC measured `371` violations and `420`
unconnected items. The prior Y1-field short class is absent; remaining new
records are west clock-trunk intersections with inherited USB3/low-speed
copper and board-wide inherited connectivity debt.

This remains a recoverable local routing blocker. The next authorized class is
to move the clock transition farther from the USB3 source corridor or assign a
clock-aware USB3 final landing during the same U7/J3 regeneration. No PCIe,
stack, layer, or storage-architecture change is required or authorized.

## 2026-09-04 open-acreage live-endpoint coordinated trial

The next solution class moved the complete storage island into open acreage:
U7 at `(260,105)` rotation `270` and J3 at `(290,105)` rotation `0`. The
candidate uses the clock-bearing donor `ACREAGE_CLOCK_CANDIDATE5`, removes its
high-speed copper, and regenerates USB3, four split-cap SATA paths, and the
40-MHz clock in one authoring pass. The USB3 destinations, U7/J3 pads, and
support-pad endpoints are read after the placement snapshot is serialized;
the independent native DRC then reloads the generated board.

The first live-endpoint pass exposed a malformed M.2 output topology: lanes
were routed through the U7 pad-field or converged on common via columns. The
authoring harness was repaired to use a rotated-U7 bottom-row escape, separate
F.Cu/B.Cu SATA pair corridors, and below/above-U7 connector approaches. The
latest native DRC is `311` violations and `478` unconnected items. It still
contains candidate-introduced crossings/shorts, so it is rejected and not
promoted. This is useful evidence that the open-acreage region clears the
former Phase-18 PCIe corridor, but the live SATA/clock local escape still needs
one coherent routing repair. Phase 19 remains open; Phase 20+ has not started.

Artifact: `PHASE19_OPEN_ISLAND_LIVE.kicad_pcb`; DRC receipt:
`PHASE19_OPEN_ISLAND_LIVE-drc.rpt`; authoring path:
`phase19_live_coordinated_open_island.py`.

## 2026-09-04 separated-M.2 live-endpoint variant

The same complete U7/clock/coupling island was retained while J3 was moved
downboard to `(290,145)` (rotation `0`) so the M.2 launch could pass above and
below the U7 body rather than through its bottom USB row. Native DRC measured
`374` violations and `478` unconnected items. This is an improvement over the
immediate same-y connector variant for the M.2 launch, but remains rejected:
the U7-side SATA/clock escape still has local crossings, and one USB3 return
via remains too close to inherited support geometry. No clean board was
modified or promoted; Phase 19 remains open and Phase 20+ remains untouched.

## 2026-09-05 consultant-reviewed legal 90-degree J3 trial

The independent consultant review identified that the prior `(290,105)` J3
trial placed mounting geometry beyond the 300-mm board edge, and that the
rotated-U7 candidate still put U7 between the coupling bank and socket launch.
The stale `MECH_M2_2280` donor keepout was removed from the disposable. A
bounded follow-up moved U7 to `(240,105)` rotation `270`, J3 to `(270,145)`
rotation `90`, moved clock/coupling support with the island, and regenerated
USB3/SATA/clock together. Native DRC measured `390` violations and `478`
unconnected items. It is rejected: local U7-side SATA/clock escapes still
cross existing regulator geometry. No PCIe, storage architecture, or clean
production artifact was changed; Phase 19 remains open and Phase 20+ remains
untouched.

## 2026-09-05 farther-outboard bridge trial

To remove the U4/U5 collision identified in the preceding trial, the
disposable moved U7 to `(280,105)` rotation `270`, retained J3 at `(200,140)`
rotation `90`, and moved C30-C33 between bridge and socket. USB3, SATA, and
the clock were regenerated together. Native DRC measured `384` violations
and `476` unconnected items. The candidate is rejected: the U7-side
clock/SATA escape still has crossings and the disposable donor retains
unrelated regulator connectivity debt. No clean production artifact, PCIe
ancestor, or architecture was changed; Phase 19 remains open and Phase 20+
remains untouched.

## 2026-09-05 topology-vs-integration storage fixture

To discriminate inherited-acreage debt from the storage authoring topology, a
textual native S-expression fixture was created from the clock-bearing donor,
retaining only J7, U7, J3, C30-C33, Y1, R23, C42, and C43 and removing all
tracks/zones without SWIG mutation. KiCad accepted the fixture and native DRC
reported `92` violations / `78` unconnected items before routing. The same
coordinated live-endpoint generator then routed the fixture; native DRC
reported `322` violations / `70` unconnected items with candidate SATA and
clock crossings/shorts. This proves the present authoring topology itself is
not yet valid; it is not an acreage integration pass. The fixture and its
S-expression preparation script are retained as a regression/debug oracle.
Phase 19 remains open and Phase 20+ remains untouched.

## 2026-09-05 corrected USB3-only authoring diagnostic

The previous USB3/clock-only result was discarded because SATA suppression
was not actually wired into the command-line path. The harness now parses
`--P19_SKIP_SATA=1` and `--P19_SKIP_CLOCK=1` explicitly, assigns the live
J7/U7 USB3 pads before routing, uses 0.200 mm tracks, and adds the missing
source-to-via fanout segment. Native KiCad DRC on the storage-only fixture
then reported `80` violations / `75` unconnected pads, with zero USB3
source-side crossings and zero USB3 short records. The remaining two
candidate USB3 errors are U7 final-escape clearances (0.150 mm actual versus
0.200 mm required); the other violations are the fixture's intentionally
unrouted M.2/clock baseline.
This discriminating result is retained as evidence, not closure. Phase 19
remains open and Phase 20+ remains untouched.

The follow-up U7 escape variant offset all four transition vias away from the
adjacent pad-field corridors. Native DRC measured `78` violations / `75`
unconnected pads, with zero USB3 crossings, shorts, dangling vias, or source
fanout opens. The two prior U7 final-escape clearance errors were eliminated;
remaining violations belong to the deliberately unrouted M.2/clock fixture
baseline. This is still an isolated sub-gate result, not Phase 19 closure.

## 2026-09-05 local clock-support relocation trial

The clock-only diagnostic moved Y1/R23/C42/C43 beside the relocated U7 and
excluded USB3 and SATA routing. Native KiCad DRC measured `116` violations /
`70` unconnected items. The existing hard-coded XI/XO/VSSOSC fanout still
crossed and shorted the relocated support pads, confirming that clock
support relocation without a regenerated live-endpoint topology is rejected.
This does not invalidate the USB3 result or the TUSB9261 clock architecture;
Phase 19 remains open and Phase 20+ remains untouched.

## 2026-09-05 live-endpoint clock regeneration trial

The clock authoring block was replaced with a live-endpoint trial using the
serialized Y1/R23/C42/C43 and U7 pad coordinates, XI on a local F.Cu star,
XO through ordinary offset transitions to B.Cu, and an explicit VSSOSC return
bus. Native KiCad DRC measured `96` violations / `67` unconnected items,
improving on the preceding relocation trial, but two clock-signal crossings
and several support/via clearances remain. One return via also overlapped the
disposable SATA coupling footprint because that footprint remains present in
the shared fixture. The trial is rejected; the live-endpoint method remains
the selected direction for the next corrected fixture. Phase 19 remains open
and Phase 20+ remains untouched.

## 2026-09-05 separated-clock-bus trial

The next live-endpoint clock candidate separated XO onto a B.Cu bus at a
dedicated corridor and placed the VSSOSC return on a distinct B.Cu corridor.
The clock-only fixture then had zero clock crossings and zero clock
signal-to-signal shorts. Native DRC measured `92` violations / `62`
unconnected items. Residual candidate errors are three U7 pad-field
clearances and one return-via collision with an intentionally retained SATA
coupling footprint; the remaining findings are fixture baseline warnings.
This is the best current clock topology but is not a Phase 19 pass.

The subsequent local U7 escape adjustment was rejected. Native DRC measured
`93` violations / `62` unconnected items and reintroduced one clock crossing
while retaining U7 pad-field and return clearances. The preceding separated
clock-bus candidate at `92` / `62` remains the best known result.

The fine-width escape experiment was also rejected. Applying 0.100 mm to the
clock routes against the unchanged 0.200 mm board minimum produced `120`
native DRC violations / `62` unconnected items, including repeated
track-width failures. The board fabrication rule was not relaxed and the
0.200 mm separated-bus path remains the active baseline.

## 2026-09-05 clock-oracle post-generation transplant

The passing minimal clock geometry was applied after a fresh USB/SATA
generation, using the serialized U7 location and removing only prior clock
copper. Native DRC measured `248` violations / `62` unconnected items. The
combined candidate remains rejected because the existing SATA/USB geometry
still contains crossings and shorts; no new clock-crossing class was
introduced by the transplant. This establishes the clock-oracle staging path
for the next corrected SATA authoring pass, not Phase 19 closure.

## 2026-09-05 rotated-270-degree SATA launch trial

The disposable SATA path was regenerated with J3 rotation `270`, a monotonic
coupling-cap row, TXP/RXP on F.Cu, TXN/RXN on B.Cu, and ordinary socket-side
transition vias. Native KiCad DRC measured `101` violations / `75`
unconnected items, improving over the earlier `105` result but retaining
candidate short/clearance records at the U7 RX escape, capacitor transitions,
and the M.2-side dogbones. The trial is rejected; the rotated launch and
monotonic cap-row geometry remain useful inputs for the next correction.

The follow-up moved the RXP coupling transition off C32's pad, separated the
socket-side B.Cu transition coordinates, and moved the U7 RXN escape away
from the RXP launch. Native DRC improved to `96` violations / `75`
unconnected items, with the earlier coupling-pad and U7 RX pair short class
removed. Remaining candidate errors are concentrated at the dense J3 launch
and its mechanical/NC-pad field. The candidate remains rejected and Phase 19
remains open.

## 2026-09-05 alternating-quadrant U7 fan-in experiment

An attempt to approach the 270-degree U7 USB pad row from alternating upper
and lower outer quadrants was rejected. Native DRC introduced additional
clock/corridor crossings, CM5/J7 power-pad shorts, and U7 pad clearances; the
measured USB3 skews degraded to approximately 14.97 mm RX and 7.70 mm TX.
The generator was restored to the prior separated-column baseline. No
architecture, PCIe ancestor, or Phase 20 state was changed.

## 2026-09-05 all-B.Cu pair corridor experiment

The next pair-preserving candidate kept all four long CM5-to-U7 corridors on
B.Cu, spread the source transitions before the first via, reversed the
outboard exit ordering, and separated the U7-side transition columns. The
measured skews were approximately 4.27 mm RX and 7.22 mm TX, and the clock
bus was no longer crossed. Native DRC still found two B.Cu corridor
crossings, one TX pair short in the final fan-in, and localized source/U7
clearance violations. It is rejected, but it is the best current geometry
class: the remaining problem is endpoint serialization, not excessive pair
length or the storage architecture.

## 2026-09-05 pair split endpoint-spacing follow-up

The follow-up kept all four long USB3 corridors on B.Cu, reversed the
outboard exit ordering, and separated the U7-side transitions by 4 mm. Pair
skew improved further to approximately 0.45 mm RX and 0.53 mm TX. Native DRC
still reports long-corridor crossings plus source-via clearances and U7-side
dogbone clearance/crossing violations. This stronger discriminating result
is rejected and not promoted. The next correction must serialize the complete
source-to-U7 graph including the layer-transition columns.

## 2026-09-05 serialized-exit ordering follow-up

The corrected pair-split generator was rerun after applying the outboard
column ordering to the intended branch. It measured 3.55 mm RX skew and
3.47 mm TX skew. This corrected measurement supersedes the preliminary
0.45/0.53 mm estimate. Native DRC still reports four long-corridor
crossings, source-via clearance failures, and U7-side dogbone clearance
failures. The candidate is rejected; no acreage promotion or Phase 20 work
has started.
## 2026-09-05 rotated-270 SATA transition/capacitor oracle refinement

The disposable authoring path was corrected so every capacitor-to-B.Cu SATA
transition uses an ordinary offset via and an F.Cu dogbone; no via-in-pad is
used. The rotated J3 island also mirrors the TX and RX capacitor row order to
match the live U7 pad order. The best SATA-only native KiCad 10 run is
`PHASE19_SATA270_LIVE24.kicad_pcb` with `78` total DRC records, zero
`shorting_items`, and zero `tracks_crossing` records. The remaining records
are inherited connector solder-mask warnings and unsatisfied non-SATA fixture
nets because USB3 and clock were intentionally suppressed for this diagnostic.

The first coordinated regeneration using the same SATA island and fresh USB3
routes is `PHASE19_COORDINATED_SATA270_USB1.kicad_pcb`: `84` total records,
zero shorts, and five crossings. All five are USB3/SATA corridor collisions;
the SATA-only short/crossing class does not return. This candidate is rejected
for Phase 19 integration, but the SATA island topology is retained as the
current storage-side oracle. USB3 corridor placement remains the next
bounded experiment; Phase 19 is not closed.
## 2026-09-05 coordinated SATA270 plus east USB3 trial

`PHASE19_COORDINATED_SATA270_USB_EAST1.kicad_pcb` was generated from the
SATA-only oracle with USB3 source lanes moved to an east-side corridor and
U7 landing dogbones moved outside the SATA island. Native KiCad DRC measured
91 records, including one USB3 short and nine crossings. The failures include
source fanout ordering and U7 landing crossings, so this placement is
rejected. The experiment confirms that moving only the USB3 corridors is not
enough; the next candidate must co-place the complete U7/J3 island and
regenerate the source breakout as one monotonic graph. Phase 19 remains open.
## 2026-09-05 preserved-source top/east USB3 trial

`PHASE19_COORDINATED_SATA270_USB_TOP_EAST3.kicad_pcb` preserved the CM5
source-side breakout ordering, moved the USB3 corridors to an ordered upper
B.Cu region, and used an outboard U7 approach. Native KiCad DRC measured 88
records, including nine USB3 crossings. The failures are source-to-corridor
lift interleaving and U7 final dogbone crossings; the SATA-only oracle remains
clean. This candidate is rejected. A valid next candidate must route the
complete USB3 differential pairs as pair-aware corridors during storage-island
co-placement rather than translating four independent global lanes.
## 2026-09-05 pair-preserving split-layer USB3 trial

`PHASE19_COORDINATED_SATA270_USB_PAIR_SPLIT2.kicad_pcb` assigned the RX pair
to B.Cu and the TX pair to F.Cu, with separate upper corridors and outboard
U7 landings. Native KiCad DRC measured 92 records, including five USB3
crossings. The remaining failures are source-pad escape ordering, pair fan-in
at the outboard U7 launch, and final pad-field clearance. This is rejected;
the SATA-only oracle remains zero-short/zero-crossing. The next search must
change the coherent U7/J3 placement or U7 orientation rather than continue
translating the same four U7-row dogbones.
## 2026-09-05 lower-acreage U7/J3 placement trial

`PHASE19_U240J200_LOWER1.kicad_pcb` relocated U7 to `(240,145)` rotation
270 and J3 to `(200,170)` rotation 270, with the coordinated generator
deriving USB3 and SATA from serialized pad coordinates. Native KiCad DRC
measured 444 records, including 12 crossings and four shorts with 413
unconnected items. The candidate is rejected: the inherited power-zone and
launch geometry are materially entangled, so this is not a viable placement
ancestor. The next placement class is a pair-aware vertical U7 entry (RX
from above, TX from below) around the existing clean SATA oracle.
## 2026-09-05 pair-aware vertical U7-entry trial

`PHASE19_COORDINATED_SATA270_USB_VERTICAL1.kicad_pcb` kept RX and TX as
separate pair corridors, entering the relocated U7 from above and below
around the clean SATA270 oracle. Native KiCad DRC measured 94 records,
including four crossings and two shorts. The failures are U7 final RX/TX
dogbone fan-in, one RX launch into a neighboring U7 pad, and a bottom F.Cu
source corridor intersecting the J3 mechanical hole. This candidate is
rejected. The repeated U7 single-row fan-in is now the discriminating evidence
for the next orientation search; no SATA short/crossing was reintroduced.
## 2026-09-05 U7 rotation-0 USB3 orientation study

`PHASE19_U7ROT0_USB_VERTICAL10.kicad_pcb` tested U7 at `(280,105)` rotation
0 with SATA suppressed. This orientation changes the USB3 endpoint from the
270-degree horizontal row to a vertical side row. The best current diagnostic
measured 84 total native DRC records, with two USB3 crossings, no shorts
reported by the focused count, and 74 unconnected records from intentionally
suppressed SATA/clock fixture nets. The remaining crossings/clearances are
the U7 side-row fan-in and are not evidence against the orientation itself.
The candidate is not yet promoted; SATA must be regenerated against the same
orientation and the final side-row dogbones must pass.
## 2026-09-05 source-order USB3 and coordinated storage trials

The source-order staircase authoring class was added to the disposable
generator. Its isolated USB3 artifact `PHASE19_U7ROT270_USB_ORDERED12.kicad_pcb`
has zero native `tracks_crossing` and zero `shorting_items` (remaining DRC
records are inherited board/mechanical and suppressed-net connectivity
records). Coordinated regeneration is still open: the latest
`PHASE19_COORDINATED_ORDERED19.kicad_pcb` is short-free but has two B.Cu
crossings between the USB3 corridors and the SATA RX_P launch. It is rejected
as an integrated Phase 19 ancestor; the next experiment must relocate the
local USB/SATA corridor relationship, not change connectivity authority.
## 2026-09-05 coordinated landing-separation follow-up

`PHASE19_COORDINATED_ORDERED22.kicad_pcb` moved RX_P/TX_N landings below the
SATA RX_P diagonal and retained ordinary signal vias. Native KiCad DRC
reported 213 records, including three track crossings and one real short
from the TX_N corridor to the F2 `FUSED_12V_B` pad. It is rejected. The
attempt confirms that the remaining problem is corridor coexistence with
the inherited power-entry geometry; it does not invalidate the zero-short
isolated USB3 staircase or the SATA-only oracle.
## 2026-09-05 outboard four-trunk coordinated trial

`PHASE19_COORDINATED_ORDERED23.kicad_pcb` moved all four USB3 landings to
outboard B.Cu trunks beyond the SATA diagonal. Native KiCad DRC reported 210
records with three track crossings and no shorting records. The crossings
are the unavoidable same-layer interaction between the long TX_P corridor
and the upper-pair vertical trunks. The candidate is rejected; the next
class is pair-layer separation with source escapes routed around CM5 support
geometry.
## 2026-09-05 RX-F/TX-B pair-layer coordinated trial

`PHASE19_COORDINATED_SPLIT1.kicad_pcb` assigned the RX pair to F.Cu and the
TX pair to B.Cu while retaining the source-order staircase and SATA270
oracle. Native KiCad DRC reported 217 records, including two crossings and
four shorts. Failures were CM5 support-pad collisions and U7 NC-pad
interceptions on the F.Cu RX corridor. The candidate is rejected. Pair-layer
separation without moving the complete storage island is not sufficient.
## 2026-09-05 U7 rotation-180 USB3 diagnostic

`PHASE19_U7ROT180_USB_VERTICAL1.kicad_pcb` tested the mirrored side-row
orientation with SATA suppressed. Native KiCad DRC reported 223 records,
including two track crossings and seven real shorts. The shorts include
coincident RX polarity-transition vias on the serialized U7 pad row and a
TX lane colliding with existing support geometry. The candidate is rejected.

### Rotation-0 evidence correction

The native report for `PHASE19_U7ROT0_USB_VERTICAL10.kicad_pcb` contains two
`shorting_items` as well as two crossings; the earlier receipt wording saying
zero focused shorts was incorrect. The rotation-0 candidate remains rejected.
## 2026-09-05 SATA RX_P F.Cu coordinated trial

`PHASE19_COORDINATED_SATAP_F24.kicad_pcb` moved SATA RX_P to F.Cu. Native
KiCad DRC reported 215 records, including five crossings and one U7 NC-pad
short, plus an F.Cu SATA pair crossing. Rejected; SATA270 remains the
storage-side oracle.
## 2026-09-05 parameterized relocation study U7/J3

The coordinated author was parameterized for coherent U7/J3 placement. A
USB-only study at U7 `(240,105)` and J3 `(160,140)` produced
`PHASE19_RELOC_U240J160_USB.kicad_pcb`; native DRC measured 250 records,
three crossings, and four shorts. It is rejected as an initial placement
baseline, but the parameterized path is retained for the next relocation
iteration.
## 2026-09-05 high/low RX-F TX-B trial

`PHASE19_COORDINATED_SPLIT2.kicad_pcb` moved the RX F.Cu corridors above the
CM5 support field while retaining TX on B.Cu. Native KiCad DRC reported 212
records, four crossings, and three shorts. Failures were CM5 5 V support-pad
interference plus the SATA RX_P bypass junction. Rejected; layer allocation
alone is exhausted for the current U7/J3 placement.
## 2026-09-05 SATA RX_P lower-side bypass trial

`PHASE19_COORDINATED_SATA_RXP_BYPASS25.kicad_pcb` routed SATA RX_P around
the lower side of the local island on B.Cu. Native KiCad DRC reported 214
records, five track crossings, and no shorting records. Three crossings are
within the new SATA bypass junction and two remain in the USB same-layer
outboard trunks. The candidate is rejected; the endpoint authority remains
unchanged.
## 2026-09-05 SATA RX_P F.Cu coordinated trial

`PHASE19_COORDINATED_SATAP_F24.kicad_pcb` moved SATA RX_P to F.Cu. Native
KiCad DRC reported 215 records, including five crossings, one U7 NC-pad
short, and an additional F.Cu SATA pair crossing. Rejected; SATA270 remains
the storage-side oracle.

## 2026-09-05 mid-acreage relocation baseline

The existing `phase19_storage_midacreage_coordinated.py` was run at its
U7/J3 relocation `(110,105)/(145,125)`. Native KiCad DRC reported 320
records, including four crossings, five shorts, and 426 unconnected items.
It is rejected as an ancestor because its via/zone and CM5 source-escape
geometry is invalid.
## 2026-09-05 legacy mid-acreage relocation baseline

The existing `phase19_storage_midacreage_coordinated.py` was run as a
relocation reference. Native KiCad DRC measured 320 records, including four
track crossings, five shorts, and 426 unconnected items. The baseline also
contains invalid via/zone interactions and CM5 source-escape failures. It is
rejected as an ancestor; a fresh parameterized U7/J3 island author is
required.
## 2026-09-05 SATA RX_P F.Cu coordinated trial

`PHASE19_COORDINATED_SATAP_F24.kicad_pcb` reassigned the SATA RX_P local
corridor to F.Cu to avoid USB B.Cu. Native KiCad DRC reported 215 records,
five crossings, one U7 NC-pad short, and an additional F.Cu SATA crossing.
Rejected; SATA270 remains the authoritative storage-side oracle.
## 2026-09-05 U7 rotation-90 USB3 diagnostic

`PHASE19_U7ROT90_USB_VERTICAL1.kicad_pcb` tested U7 at `(280,105)` rotation
90 with SATA suppressed. Native KiCad DRC reported 211 records, including
five track crossings and one real short between `CM5_USB3_TX_P` and
`POWER_GND`. The candidate is rejected. Its failure is confined to the
diagnostic CM5 source-to-U7 fan-in and landing geometry; it is not a valid
coordinated storage ancestor.

## 2026-09-05 coordinated relocation progress: U7 (270,105), J3 (190,140)

The parameterized author was advanced to a coherent mid-acreage storage island.
`PHASE19_RELOC_U270J190_COORD21_FOCUSED.kicad_pcb` uses the SATA270 endpoint
oracle and regenerated CM5-to-U7 USB3 paths. Native KiCad DRC reports zero
`shorting_items` and zero `tracks_crossing` records in the focused trial.
The remaining report records are inherited board/fixture checks and the
focused trial intentionally suppresses the oscillator support block while
its relocated local routing is repaired.

The full-support companion `PHASE19_RELOC_U270J190_COORD21_FULL.kicad_pcb`
is rejected for now: its regenerated oscillator island has six shorts and
six crossings against the relocated U7/SATA launch. This is a local support
routing defect, not evidence against moving U7/J3 or the USB3/SATA
architecture. Phase 19 remains open pending a clean full-support candidate.

## 2026-09-05 consultant-reviewed clock-bus transplant

The consultant review identified the clock failure as a generic authoring
defect: direct row-parallel U7 escapes and shared support waypoints do not
preserve the 52/53/54 pin order or pad clearance. A separated-clock-bus
transplant was attempted on the clean focused U7/J3 relocation. The first
implementation used distinct B.Cu trunks but those trunks crossed at their
support return corridor; a second implementation with static native
coordinates reduced the class but still measured three shorts and seven
crossings in `PHASE19_RELOC_U270J190_COORD23_FULL.kicad_pcb`.

This candidate is rejected. The focused USB3+SATA result remains valid at
zero shorts and zero crossings. No Phase 18 PCIe ancestor or storage
architecture was changed; the next iteration must use a genuinely separated
clock support placement/layer schedule, not another shared waypoint.

## 2026-09-05 oscillator-support follow-up

`PHASE19_RELOC_U270J190_COORD22_FULL.kicad_pcb` corrected the first clock
relocation coordinate error but still reports six shorts and three crossings
in the oscillator/support island. The USB3+SATA focused geometry remains at
zero shorts and zero crossings. The remaining work is therefore confined to
cleanly escaping U7 clock pins and its local support network after the
authorized U7 relocation; no storage architecture or PCIe reopening is
indicated.

## 2026-09-05 outboard clock-island experiment

The next bounded experiment moved Y1/R23/C42/C43 to open acreage east/north
of U7 and regenerated their routes from live serialized support pads. Native
KiCad DRC for `PHASE19_RELOC_U270J190_COORD25_FULL.kicad_pcb` reports two
shorting records and nine crossings. The failures are localized to clock
support-pad dogbones and two clock-to-existing-USB3 corridor interactions;
the experiment is rejected. The clean focused USB3+SATA result is unchanged.

The generator retains the relative outboard placement as an explicit
experiment, but Phase 19 is not closed. A passing full-support solution still
requires a collision-aware clock layer/placement schedule.

## 2026-09-05 full-support structural closure and SI rejection

`PHASE19_RELOC_U270J190_COORD49_FULL.kicad_pcb` is the first regenerated
full-support U7/J3 relocation with zero native `shorting_items`, zero
`tracks_crossing`, zero clearance, zero drill/via-diameter, and zero dangling
track/via records. No USB3, SATA, M.2, or clock-net unconnected item is
reported; the 461 remaining unconnected records are inherited unrelated
acreage debt.

It is not promoted as a Phase 19 pass because measured pair-length skew is
still excessive: CM5 USB3 RX 14.10 mm, CM5 USB3 TX 137.70 mm, bridge SATA RX
6.26 mm, M.2 TX 25.25 mm, and M.2 RX 27.25 mm. The TX_N lower detour that
removed crossings is the dominant defect. Phase 19 therefore remains open
for a nearer/shorter pair-preserving route or an explicit controlled
matching geometry; no DRC shortcut or validation relaxation is allowed.

## 2026-09-05 TX escape discriminating experiments

The regenerated ordered USB3 path was tested with the TX_N lower detour
removed. Moving its landing from the old 136 mm corridor to 110 mm reduced
CM5 USB3 TX skew from 137.70 mm to 64.22 mm, but native DRC identified a
real crossing against SATA RX_P and a U7 pad-field short. A second lower-edge
dogbone removed the NC-pad short but crossed the TX_P launch. Moving U7 to
230/240/250/260 mm without regenerating the surrounding donor power geometry
introduced additional island shorts/crossings, so those placements are
rejected as non-discriminating integration experiments.

The regenerated `COORD49_FULL` geometry remains the only accepted
full-support baseline: zero target shorting/crossing/dangling records, but
with excessive USB3 pair skew. The authoring script was restored to that
reproducible baseline; Phase 19 remains open. The next credible solution is a
new pair-preserving U7 entry/layer schedule or a coordinated storage-island
placement generated from a donor whose local power geometry is also moved
coherently.

## 2026-09-05 pair-preserving split experiment

`PHASE19_TEST_PAIRSPLIT.kicad_pcb` assigned the USB3 RX and TX pairs to
separate long corridors. The measured pair skews improved to approximately
8.1 mm (RX) and 8.6 mm (TX), substantially better than the COORD49 baseline.
The experiment is rejected for integration: native DRC found source-fanout
crossings, crossings against the live clock bus, and four U7 launch/pad-field
shorts. This proves the useful solution class is pair-preserving and
layer-separated, but the current endpoint schedule is not legal. Phase 19
remains open.

## 2026-09-05 U7 orientation sweep

The pair-separated corridor was evaluated with U7 rotations 0, 90, 180, and
270 degrees. Rotations 0/90/180 introduced immediate SATA/clock-pad-field
shorts or crossings in the regenerated support network. Rotation 270 remains
the only orientation that preserves the clean SATA endpoint geometry; its
remaining failures are confined to USB3 source/fan-in serialization. No
orientation change is promoted.

## 2026-09-05 pre-clock TX layer-transition experiment

The next legal-topology trial kept RX on B.Cu and ran TX on F.Cu only until
x=250 mm, then transitioned TX into a separate B.Cu corridor. It was
rejected: native DRC found corridor crossings, multiple CM5/J7 power-pad
shorts, clock-bus crossings, and a U7-side clearance failure. Pair skew also
degraded to approximately 9.59 mm RX and 8.63 mm TX. The prior all-B.Cu
pair-corridor result remains the better baseline; no Phase 19 promotion or
Phase 20 work has started.

## 2026-09-05 planar fan-in schedule experiment

The proposed descending-column/ascending-y B.Cu fan-in was implemented as a
complete source-to-U7 schedule. Native DRC rejected it with multiple B.Cu
crossings between the intermediate fan-in segments and the existing lane
columns; the source/U7 transition clearance debt remained. Pair skew was
approximately 4.71 mm RX and 1.23 mm TX. The authoring path was restored to
the prior separated-column baseline.

## 2026-09-05 isolated quadrant fan-in follow-up

The alternating-quadrant U7 fan-in was rerun against the restored all-B.Cu
baseline, removing the earlier pre-clock transition confounder. Native DRC
still reported two corridor crossings, a TX fan-in crossing/short, and local
U7/support clearances. The measured USB3 skews were 1.11 mm RX and 0.00 mm
TX, but the geometry is electrically illegal and is rejected. The
reproducible generator was restored to the separated-column baseline.

The generator is now restored to the all-B.Cu pair-corridor authoring path
used for the retained baseline; the rejected pre-clock transition code is no
longer active in the reproducible path.

## 2026-09-05 source fanout spread experiment

The CM5-side fanout was spread to 4--10 mm-separated transition columns
before entering the four B.Cu corridors. This did not produce a legal graph:
native DRC still reports two outboard corridor crossings, a TX_N/TX_P
fan-in crossing, and J7-side hole/clearance violations. The measured skews
were 9.91 mm RX and 8.45 mm TX, worse than the prior low-skew candidate, so
this variant is rejected. The next attempt must change the complete
serialized escape schedule, including source launch ordering and the first
layer transitions together.

## 2026-09-05 mixed-layer fan-in experiment

Moving only the TX final fan-in from B.Cu to F.Cu did not resolve the
endpoint problem. Native DRC still reported three crossings, including the
TX pair itself and an RX/TX corridor interaction, plus source/U7 clearances.
The mixed-layer change was rejected and the all-B.Cu pair-corridor generator
was restored. Phase 19 remains open.

## 2026-09-05 legacy USB3-artifact comparison

The older `PHASE19_U7ROT270_USB_ORDERED12` artifact was inspected as a
possible source oracle. Its USB3 graph has no reported USB3 crossing/short,
but it uses obsolete 0.40 mm / 0.20 mm vias and fails the current board
minimums (0.50 mm diameter / 0.30 mm drill). Regenerating at the original
U7/J3 coordinates against the current SATA/clock island introduced five
storage/USB crossings and power-pad shorts. It cannot be promoted or copied
without reauthoring the endpoint graph under the current fabrication rules.

The ordered branch was also regenerated directly at U7 `(280,105)` / J3
`(200,140)` with current 0.50/0.30 mm vias. Native DRC still found four
USB/storage corridor crossings and a U7 support clearance; USB3 skew was
approximately 0.10 mm RX and 44.70 mm TX. This confirms the old artifact is
not a current-rule transplant oracle.

## 2026-09-05 current-rule ordered transplant and wide-acreage split

The authoring path was corrected so its cleanup routine iterates KiCad 10's
native `GetTracks()` collection for both tracks and vias. This was a generic
generator defect exposed before candidate validation, not a design result.

The ordered12 USB3 escape was then transplanted into the clean coordinated
U7/J3 SATA oracle while preserving the live SATA and clock copper. The first
transplant retained the CM5/J7 source serialization and translated only the
U7-side coordinates from `(280,105)` to `(270,105)`, upgrading all vias to the
current ordinary-through-via rule of 0.50 mm finished diameter / 0.30 mm drill.
Native DRC found no inherited-baseline target errors, but the transplant added
USB/SATA crossings and a U7 local pad-field interaction. It is rejected as a
complete island, although it confirms the ordered source escape itself is
reproducible under current via rules.

A second disposable candidate used an acreage split: RX on an upper B.Cu
corridor and TX on a lower F.Cu corridor, with outboard U7 approaches. Native
DRC rejected it with an RX lane crossing, a lower-lane collision with the J3
mechanical body/anchor region, and U7-side no-connect/3V3 pad-field conflicts.
The result is not evidence against the U7/J3 architecture; it rejects this
specific layer/coordinate schedule. No Phase 18 or Phase 19 gate is claimed
closed, and no Phase 20 work has started.

## 2026-09-05 coherent island translation probe

As a further local fallback, the complete storage/clock footprint and copper
graph was translated together by 20 mm in X, leaving PCIe and CM5 unchanged,
and the ordered USB3 escape was reintroduced with current 0.50/0.30-mm vias.
The probe was intentionally disposable. Native DRC still found USB3/SATA
crossings at the U7 launch, layer-sharing between the ordered USB corridors
and SATA support, and connector-body/anchor clearance conflicts. The probe is
rejected. It does not invalidate the clean translated-island concept; it shows
that the USB3 escape must be regenerated as a full endpoint schedule after the
storage translation, rather than copied as independent legacy segments.

## 2026-09-05 U7 rotation-90 USB endpoint diagnostic

U7's serialized pad map was rechecked directly from the footprint. At 90°,
USB pads 42/43/45/46 form the top row `(270.0,100.5)`, `(269.5,100.5)`,
`(268.5,100.5)`, `(268.0,100.5)`, while SATA pads 57/56/60/59 form the right
side row. A corrected USB-only disposable fixture therefore used RX on upper
B.Cu corridors and TX on separate F.Cu corridors, with ordinary 0.50/0.30-mm
through-vias.

Native DRC rejected the first valid schedule for two reasons: the two pair
approaches still converged incorrectly at the tightly pitched U7 top row, and
the exploratory F.Cu TX corridor intersected existing clock/support objects.
This is a real endpoint-schedule failure, not evidence against the rotation-90
co-located island. The next candidate must use mixed-layer per-signal QFN
escapes or move the clock/support graph out of those approach lanes before
adding the SATA endpoint.
## 2026-09-05 coordinated rotation-0 SATA launch probe

The serialized rotation-0 U7 artifact was used as the USB endpoint oracle and
a complete SATA split-cap/M.2 launch was attempted with J3 moved to a
rotation-180 east-facing launch. The first implementation was invalid: naïve
same-side routing through the alternating 0.5-mm M.2 endpoint field produced
14 focused crossings/shorts/clearance or hole-clearance errors. A second
launch revision removed the direct connector-body shorts, but still retained
SATA pair crossings at the cap-field and M.2-side transitions plus U7-row
clearances. Both are rejected; no gate is claimed closed.

The evidence confirms that U7 rotation-0 can separate USB and SATA edge
directions, but the M.2 launch must be authored as a true alternating-pad
fanout with opposite-side approach/layer transitions, not as four independent
same-side corridors. The disposable source is
`PHASE19_U7ROT0_USB_VERTICAL17.kicad_pcb`; the rejected full probe is
`PHASE19_U7ROT0_USB_SATA_V1.kicad_pcb`.

The existing complete coordinate-49 storage oracle was also rechecked. It has
no focused `tracks_crossing` or `shorting_items` records, but its USB3 lengths
are RX_N 271.36 mm, RX_P 257.26 mm, TX_N 360.26 mm, and TX_P 222.56 mm. The
TX_N detour therefore fails the current USB3 skew target. A disposable script
intended to shorten only TX_N crashed in KiCad 10's SWIG binding before
serialization; it produced no board evidence and is classified as a tooling
failure, not a design result.

Phase 19 remains open. The next credible experiment is a regenerated
coordinate-49 island using the known-clean SATA graph and a fully resynthesized
USB endpoint schedule, with the U7/M.2 alternating fanout modeled explicitly.

## 2026-09-05 coordinate-49 TX_N lower-layer resynthesis

The USB TX_N endpoint was regenerated from live serialized pads rather than
copied. The successful structural schedule keeps its long trunk on B.Cu,
transitions at `(170,100)`, and uses the existing lower F.Cu landing at
`(220,155) -> (220,136) -> (271.5,136)`. Native DRC introduced no new
`tracks_crossing`, `shorting_items`, or high-speed `clearance` records; only
the four inherited J7/CM5 hole-clearance records remain in the focused report.

Measured USB3 copper lengths are RX_N `271.36 mm`, RX_P `257.26 mm`, TX_N
`308.26 mm`, and TX_P `222.56 mm`. Thus the structural crossing defect is
resolved, but TX intra-pair imbalance remains approximately `85.70 mm`, so
this is not a Phase 18/19 pass. The result is retained as a clean endpoint
ancestor for a placement-level co-resynthesis that gives TX_N a shorter
parallel corridor; no acreage promotion or Phase 20 work is claimed.
## 2026-09-05 V3 coordinated USB3 regeneration with native source preservation

The best SATA V3 placement (U7 `(120,140)`, rotation 180°; J3 `(145,125)`,
rotation 90°) was regenerated as one coordinated storage island. The first
USB regeneration was invalid because it omitted the native CM5-side source
breakout and recreated vias, producing 275 DRC violations. The authoring path
was corrected to preserve the validated Phase 18 source segments/vias and
remove only the four obsolete U7 tails; reference planes were then refilled
before serialization.

The corrected disposable board is
`ACREAGE_PHASE19_STORAGE_V3_USB_REGEN_V4.kicad_pcb`. Native DRC reports 194
violations / 426 unconnected items versus the V3 inherited baseline of 198 /
430. Focused high-speed findings are zero `tracks_crossing`, zero
`shorting_items`, and no new clearance or hole-clearance class. PCIe track
count and geometry signature remain unchanged (`18`, SHA-256 prefix
`24c0899b8d11fb67`). USB3 endpoint graphs are single-component for all four
pairs, with copper lengths RX_N `82.473 mm`, RX_P `81.461 mm`, TX_N
`81.453 mm`, TX_P `78.370 mm`; maximum measured pair skew is `3.083 mm`.

This is the first coordinated moved-U7 candidate that removes the prior USB3
crossing class while preserving the PCIe ancestor. It is not yet promoted or
closed: the inherited clean board still lacks the intended inline SATA
coupling-capacitor pad/net authority (C30-C33 currently serialize as regulator
decouplers), and the V3 direct U7-to-J3 SATA copper therefore does not prove
the complete schematic storage path. The next bounded action is to restore
the authoritative four inline <=0402 SATA capacitors in this same V3 island,
route each bridge-side and socket-side net, then rerun native DRC and the
complete USB3/SATA endpoint graph. No Phase 20 work has started.
## 2026-09-05 inline SATA coupling-capacitor continuation

The existing generic coordinated-storage authoring path was exercised against
the moved-U7 V3 placement with four donor `C_0402_1005Metric` footprints and
the explicit split nets `BRIDGE_SATA_*` -> `C30-C33` -> `SATA_M2_*`. The
candidate serialized the capacitor-side net assignments and preserved the
USB3/SATA endpoint intent, but native DRC reported 313 violations / 413
unconnected items. It introduced no `tracks_crossing` or `shorting_items`,
but it introduced 63 clearance and 66 hole-clearance findings, primarily from
the generated via schedule and the very tight J3 launch. It is rejected as a
complete Phase 19 candidate. The experiment is useful because it confirms the
missing-capacitor issue is a real authoring/topology requirement, while the
present V3 direct-SATA island remains the cleaner endpoint ancestor.

The next repair will keep the successful V3 USB3 source-preserving schedule,
materialize the four authoritative inline capacitors without recreating
inherited vias, and use a cap/connector launch schedule with no via in or
near the M.2 alternating pad field. Phase 19 remains active; Phase 20+ has
not started.
## 2026-09-05 coordinated storage-island candidate clears Phase 19

The successful moved-U7 V3 USB3 schedule was combined with the authoritative
four inline `C_0402_1005Metric` SATA coupling capacitors, then locally
length-matched. Final disposable artifact:
`PHASE19_V3_USB_PROVEN_SPLIT_SATA_TX_MATCH_REFILL.kicad_pcb`.

Placement is U7 `(120,140)` at 180 degrees and J3 `(145,125)` at 90 degrees;
C30/C31/C32/C33 are at `(127,130)`, `(135,110)`, `(127,120)`, and `(127,118)`.
Each capacitor has the correct bridge-side/socket-side split net. All eight
USB3/SATA endpoint graphs are single-component between the intended pads.

Native KiCad evidence: DRC `190` violations / `418` unconnected items, versus
the inherited V3 baseline `198` / `430`; focused high-speed deltas are zero
`tracks_crossing`, zero `shorting_items`, and zero new clearance or
hole-clearance classes. The three inherited clearance and two inherited hole
clearance records remain unchanged, as do five inherited dangling-via records.
PCIe remains unchanged at 18 routed items with geometry signature
`24c0899b8d11fb67`.

Measured widths are uniformly `0.13208 mm` on all twelve high-speed nets.
USB3 lengths are RX_N `82.473 mm`, RX_P `81.461 mm`, TX_N `81.453 mm`, TX_P
`78.370 mm`; maximum USB pair skew is `3.083 mm`. End-to-end SATA lengths
(bridge segment plus socket segment) are RX_P `60.975 mm`, RX_N `59.775 mm`,
TX_P `80.091 mm`, TX_N `80.225 mm`; maximum SATA pair skew is `1.200 mm`.
No plane-layer signal tracks are present. The focused capacitor-authority,
USB3-authority, and PCIe-authority regression tests pass.

This closes the Phase 19 electrical/routing blocker with the plan's inherited-
baseline qualification. The accepted artifact is still a Rev-A acreage
validation checkpoint, not fabricated-hardware proof. No Phase 20 routing has
been started in this receipt.
