nova-rey/pisxme/blocker.md

# PiSXMe Rev A Clean — Blocker Report

## Current update — 2026-09-04

The latest bounded trial moved the authoritative EDAC MagJack to the open
right edge at `(282.5,53)` while retaining the accepted CM5IO-derived ESD
island. `phase17_right_edge_mdi_trial.py` regenerated all eight MDI nets with
distinct ordinary through-via lanes on F.Cu/B.Cu. Native KiCad DRC rejected
the trial with 332 violations and 447 unconnected items, including
Ethernet-specific pair crossings/shorts at the existing acreage copper and
ESD escape. This is a rejected routing-generator result, not evidence that
the right-edge placement or CM5IO topology is impossible. The next
authorized class is a genuinely fresh source-to-ESD island in open acreage
with an explicit no-go mask for frozen PCIe and power copper.

Evidence is pushed in commit `1cd2a44` and in
[`PHASE17_MECHANICAL_REOPEN_RECEIPT.md`](pisxme/reva-clean/PHASE17_MECHANICAL_REOPEN_RECEIPT.md).

The subsequent fresh open-acreage island trial moved U9/U6 to `(205,140)` /
`(215,140)` and J2 to `(282.5,140)`. Native KiCad DRC reported 285 violations
and 445 unconnected items. This removed the historical island-placement
collision but rejected the generated source lanes because they crossed the
existing F2/power-entry corridor and the ESD package breakout. It remains
recoverable evidence, not terminal `BLOCKED`; the next attempt uses an
outboard edge launch with explicit no-go geometry.

The subsequent west-perimeter launch trial placed U9/U6 at `(220,25)` /
`(230,25)` and J2 at `(282.5,25)`, routing around the board perimeter. Native
KiCad DRC reported 272 violations and 449 unconnected items, including
Ethernet pair crossings/shorts in the ESD fanout and edge launch. This third
class is rejected as manual lane geometry; Phase 17 remains active and the
CM5IO-derived architecture remains authoritative.

The package-row dogbone correction reduced neither the acceptance risk nor
the gate failure: native DRC now reports 289 violations and 453 unconnected
items, with crossings/shorts at the interleaved J7 fanout and ESD launch. The
result is preserved in the same west-perimeter candidate and remains
recoverable; no Phase 18 work has begun.

The prior uniform-cooler-courtyard assumption has been removed from the
disposable Phase 17 authoring path. `MECH_V100` remains a visible measured
cooling/backplate datum, but is no longer a universal hard collision volume.
The corrected trial reduced native DRC from 216 to 188 and removed all
`MECH_V100` courtyard collisions. Ethernet scoped regression and route
metrics still pass: zero Ethernet crossings/shorts and 0.547–0.829 mm pair
skews.

This is a recoverable Phase 17 placement blocker, not a terminal design
failure. The next authorized experiment is a split island: keep ESD/source
support near CM5, place the tall MagJack at an open board edge, and validate
the regenerated connector launch against real body, latch, and service
clearance. Phase 18 remains correctly gated.

Evidence and implementation are in commit `f3fbaa7` and
[`PHASE17_MECHANICAL_REOPEN_RECEIPT.md`](pisxme/reva-clean/PHASE17_MECHANICAL_REOPEN_RECEIPT.md).

## Final state

`PISXME_REVA_CLEAN_RECOVERABLE_PHASE17`

## Earliest failed gate

Phase 17 — Ethernet routing.

Phases 0–16 are not the current blocker. Phase 3 schematic/library authority
is closed, and Phase 16 PCIe routing is closed with its documented bounded
Rev-A empirical risk.

## Blocking condition

The Phase 11/12 placement is frozen with the CM5 Ethernet source at J7 near
the left side and the Ethernet ESD and MagJack at the right edge, separated by
the V100 cooler reservation and existing regulator, power, PCIe, and connector
keepout geometry.

Under the approved six-layer contract—F.Cu primary signals, In1/In4 solid
ground, In2/In3 power, B.Cu secondary signals, ordinary through-vias, and no
ordinary signals on plane layers—the frozen placement does not admit a short,
monotonic, no-maze Ethernet route.

## Evidence

- Latest native KiCad DRC candidate: `pisxme/reva-clean/CM5IO_J7_CM5IO_BOUNDARY_FIXTURE-swap5-drc.rpt`
- Latest disposable bridge report: 247 total violations, including 4
  track crossings, 78 unconnected items, 16 dangling tracks, and 2 dangling
  vias. This is the current remote-island permutation trial; it does not
  replace the independent official-fixture or J7-launch evidence.
- Representative Ethernet failures include CM5 pair crossings at J7,
  pair shorts near U6/U9, crossings against existing power/regulator tracks,
  NPTH hole-clearance violations at J7/F2/J2, and ESD pad-field clearance
  violations.
- Tested variants included perimeter routing, separated B.Cu corridors,
  via-in-pad transitions, and compact ESD placements. None passed the Phase 17
gate.

## Layer-separated 180-degree launch refinement — 2026-09-03

The isolated 180-degree fixture was refined using measured failure data.
TD2/TD0 and the right-side source groups were moved to B.Cu through ordinary
through-vias; via centers were increased to approximately 0.8 mm separation
where the previous trial had 0.5 mm clearance failures. No plane-layer
signals or via-in-pad transitions were used.

Native KiCad DRC improved from 192 to **163 violations**, with **3
unconnected items**, but still rejects the fixture. Remaining failures
include B.Cu tracks crossing other MDI routes, J2 through-hole/route
collisions, and residual J7/ESD transition clearances. This is a bounded
refinement, not Phase 17 closure. The updated fixture and report remain at
`CM5IO_ROT180_WEST_FIXTURE.kicad_pcb` and
`CM5IO_ROT180_LAYER_SPLIT_FIXTURE-drc.rpt`.
- No rejected candidate was accepted as production routing.

## Authority status

Closed:

- Native Ethernet hierarchy and eight MDI-pair connectivity.
- EDAC `A70-112-331N126` manufacturer pad mapping.
- Complete logical-pin to physical-pad aliases for all 18 MagJack contacts.
- Native PCB mapping regression.
- CM5/J7, ESD, and MagJack net authority.

Relevant commits:

- `490ae22` — EDAC physical pad alias correction.
- `ce62f86` — Phase 17 routing rejection and blocker record.

## Impact

Phase 17 cannot close. Phase 18 USB3, Phase 19 SATA, final acreage freeze, and
external-review-ready status must not begin or be claimed.

No accepted routed design was pushed, fabricated, ordered, or published.

## Best practical resolution

Reopen the Phase 11/12 placement decision and create a compact CM5-adjacent
Ethernet island containing J7 breakout, ESD protection, EDAC MagJack, and local
shield/return and center-tap circuitry. Then regenerate and revalidate affected
downstream phases before retrying Phase 17.

Routing Ethernet on power/ground plane layers or accepting the current maze
would violate the approved plan and is rejected.
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
