nova-rey/pisxme/CAPABILITY_MAP.md

# KiCad / Codex capability map

Inventory date: 2026-08-20

## Detected installation

- KiCad application: `/Applications/KiCad/KiCad.app`
- KiCad version: `10.0.5` (from `Contents/Info.plist` and bundled `kicad-cli --version`)
- Bundled CLI: `/Applications/KiCad/KiCad.app/Contents/MacOS/kicad-cli`
- `kicad-cli` is not currently on the shell `PATH`.
- Global KiCad preferences: `/Users/Cooper/Library/Preferences/kicad/10.0/kicad_common.json`
- IPC setting was initially disabled. It is now enabled as an authorized integration prerequisite.

## Supported live IPC path

The official `kicad-python` package is installed in the project Python 3.11 environment:

- Python: `/usr/local/opt/python@3.11/bin/python3.11`
- Environment: `.venv311`
- Binding: `kicad-python==0.7.1`
- Binding API build: `10.0.1-0-g2db9e5a72b`
- Dependencies: `protobuf`, `pynng`
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
