nova-rey/pisxme/pisxme/reva-clean/PHASE24_COMPONENT_PARITY_RECEIPT.md

# Phase 24 component reference-set receipt

The native KiCad netlist `PHASE24_NETLIST_FINAL5.xml` contains 78 electrical
component references. The disposable
`PHASE24_ALL_AUTHORITATIVE_PARTS.kicad_pcb` contains those 78 references plus
the explicitly classified legacy/test/mechanical extras:

- `CCT`, `CCT1`--`CCT4`, `RCT1`--`RCT4`: legacy Ethernet center-tap/resistor
  aliases, not present in the clean schematic source;
- `MECH_M2_2280` and `TP1`--`TP13`: mechanical/test markers.

`phase24_full_reference_set_audit.py` passes this exact set comparison. This
receipt proves component-reference materialization only. It does not claim
pad-net parity for the entire board or routed Phase 24 closure.
