nova-rey/pisxme/pisxme/reva-clean/authority-inventory/rtl9210b/RTL9210B_REFERENCE_PACKAGE_LEAD.md

# RTL9210B reference-package recovery lead

Checked: 2026-09-06.  This is a source-recovery receipt, not application
authority.

The 21ic resource listing advertises a package titled “RTL9210B reference
schematic” and lists the following files:

- `RTL9210B_Power_Consumption_Report_v1.0.pdf`
- `RTL9210_9210-VB_9210B_Reference_Schematic_V004.{DSN,pdf,sch}`
- `RTL9210_9210-VB_9210B_Reference_Schematic_V008.{DSN,pdf,sch}`
- `RTL9210_Layout_Guide_1.0.pdf`

Source: <https://dl.21ic.com/download/9210_reference_dsn-720866.html>.

The page is a third-party user-uploaded listing, not a Realtek-hosted
release. The download link redirects to a login-gated 21ic endpoint in the
current environment, so the files were not silently treated as retrieved or
authoritative. Their advertised existence is useful for the next evidence
recovery attempt because it could contain the missing power-consumption,
application-circuit, and layout guidance artifacts.

Current disposition:

- not copied into the repository;
- not used to choose support values or M-key wiring;
- not sufficient to close B1/B2/B4/B5;
- human action if desired: obtain the package through a legitimate 21ic
  account or from Realtek/OEM/FAE, then record hashes and provenance before
  design use.
