nova-rey/pisxme/pisxme/reva-clean/authority-inventory/primary-docs/power/TPSM63606_SUPPORT_AUTHORITY.md

# TPSM63606RDLR support-network authority

Checked: 2026-08-30. Status: `CLOSED_FOR_PHASE15_LAYOUT_AUTHORITY`.

## Primary authority

The governing source is the locally preserved TI `TPSM63606` revision B
datasheet: `../TPSM63606.pdf` (SLVSGB4B, revised April 2022).

The pin descriptions on datasheet pages 3–4 require VIN1/VIN2 to be supplied
and locally bypassed, VLDOIN to be biased from an output point or otherwise
handled per the voltage condition, AGND to be joined to PGND, VOUT1/VOUT2 to
feed the output capacitors, FB to use an external divider, RT to use an
external resistor to AGND, PG to use a 10 kOhm–100 kOhm pull-up, and EN/SYNC
to have an explicit high/low or UVLO policy. CBOOT/RBOOT are optional slew
rate-control connections around the internal 100-ohm bootstrap path; they are
not a license to place a general signal on SW.

The TI reference table on datasheet page 17 establishes these design points;
the 5-V reference design on page 24 uses two 47-uF ceramic output capacitors:

| Rail | RFBT with RFBB = 10 kOhm | Suggested FSW | Minimum effective COUT | CFF |
|---|---:|---:|---:|---:|
| 5.0 V | 40.2 kOhm | 0.8–1.2 MHz | 30 uF | 22 pF; TI example is 2 x 47 uF |
| 3.3 V | 23.2 kOhm | 0.7–0.95 MHz | 50 uF | 47 pF |
| 1.0 V | short | 0.3–0.5 MHz | 300 uF | none |

The 1.1 V rail is not a table row. Rev A must not silently interpolate the
1.0 V row: its FB/FSW/COUT choice remains an explicit engineering calculation
before the Phase 5 gate can close.

## Procurement basis

For the 10-uF, 50-V input ceramic family, TI lists TDK
`C3216X7R1H106K160AC`, but current DigiKey search evidence showed it on
backorder. It is therefore not selected as a single-source production
dependency.

For the 22-uF output ceramic listed by TI, TDK
`C3225X7R1C226M250AC` is selected: 1210, 22 uF, 16 V, X7R, ±20%, with the
same assembly geometry and an official TDK characteristic sheet. TDK's
current product page reports 41,593 DigiKey pieces, 48,825 Mouser pieces,
118,000 Avnet Abacus pieces, and 132,000 Arrow pieces in the current snapshot;
DigiKey lists cut tape at approximately $0.73 quantity-1 and $0.31 at 1,000.
Minimum order is one cut-tape part; reel packing is 1,000 pieces. DigiKey
marks the part active and it supports reflow assembly and ordinary 1210
placement.

The earlier Murata `GRM32ER71C226KEA8K` candidate is rejected for lifecycle
risk: Mouser currently flags it as scheduled for obsolescence/EOL even though
some distributor stock remains. It is not the Rev-A BOM authority.

The detailed local TDK provenance receipt is
`TDK_C3225X7R1C226M250AC_AUTHORITY.md`.

TI's public EVM reference is preserved locally as
`TPSM63606_EVM_User_Guide.pdf` and the original `SLVRBI7` design archive as
`TPSM63606_EVM_Layout_Files_SLVRBI7.zip`. The EVM guide documents four 47-uF
output capacitors with 110 uF effective at 5 V/25 C and provides the source
layout/assembly figures used for the Phase 15 overlay review. The EVM is a
2-oz four-layer reference, so its thermal and impedance results are not
silently transferred to Rev A's JLC board.
Archive SHA256: `7ddcb1b8754445c99459b9e2eed72d6c4b833b3c0a7efcd6ad98f764ecffeb0c`.

The simplest always-on EN/SYNC policy is direct connection to VIN. PG is an
open-drain output and needs a separate 20–100 kOhm pull-up; it must not be
merged with EN. The internal 100-nF bootstrap capacitor and 100-ohm resistor
mean CBOOT/RBOOT should remain open unless slew-rate tuning is intentionally
calculated. VCC is an internal LDO output and must not be externally loaded.
AGND pins 6/11 join PGND pin 19 under the module; PGND 17–20 are the power
return and thermal path.

The 0402 feedback, RT, EN, and PG resistors may use a mainstream thick-film
family such as Yageo `RC0402FR-0710KL` for 10 kOhm, with exact value variants
selected from the same family after the rail calculations. This is a
procurement-friendly placeholder family, not yet a closed exact BOM choice.

Sources checked for the current procurement snapshot:

- TI primary datasheet: `https://www.ti.com/lit/ds/symlink/tpsm63606.pdf`
- TDK product page:
  `https://product.tdk.com/en/search/capacitor/ceramic/mlcc/info?part_no=C3225X7R1C226M250AC`
- TDK characteristic sheet:
  `https://product.tdk.com/en/system/files/dam/doc/product/capacitor/ceramic/mlcc/charasheet/c3225x7r1c226m250ac.pdf`
- DigiKey listing:
  `https://www.digikey.com/en/products/detail/tdk/C3225X7R1C226M250AC/1587497`
- Mouser listing:
  `https://www.mouser.com/ProductDetail/TDK/C3225X7R1C226M250AC`

## Exact PiSXMe decision

The clean `TPSM63606RDLR_RDL0020` footprint now follows the TI RDL0020A
datasheet land-pattern arrangement: pins 1-16 are perimeter lands and pins
17-20 are the four central PGND thermal lands. The TI layout guidance is the
Phase 15 overlay authority: symmetric VIN/VOUT capacitor placement, short FB
route, local top-side PGND copper, and a 0.3 mm thermal-via array to the
adjacent ground plane. Exact rail values and DC-bias derating remain recorded
Phase 5 design inputs; this receipt closes the package/layout authority needed
for Phase 15 routing.

License/provenance: TI material is retained for design-reference use under the
TI datasheet terms; TDK characteristic data is retained as manufacturer
design-reference material; distributor pages are procurement evidence only.
The TDK replacement uses the existing generic 1210 footprint and requires no
third-party CAD asset.
