nova-rey/pisxme/pisxme/reva-clean/authority-inventory/primary-docs/service-usbc/10171746-00021LF_AUTHORITY.md

# USB-C SERVICE connector authority — Amphenol 10171746-00021LF

Checked: 2026-08-30. Status: `CLOSED` for the Rev-A USB2 UFP connector.

## Candidates considered

| Candidate | Evidence | Disposition |
|---|---|---|
| Amphenol `10171746-00021LF` | Manufacturer product page and drawing `10171746`; USB 2.0, 16P, top-mount right-angle SMT | **Selected** |
| GCT `USB4105-xx-A-16P` | CM5IO donor library candidate; no exact clean-board mechanical need | Rejected: less direct authority for the selected 6.5 mm body and no reason to change |
| Generic low-cost USB-C 16P receptacles | Parametric alternatives | Rejected: connector shell/stake geometry and footprint would require a new mechanical contract |

## Selected item

- Exact MPN: `10171746-00021LF`, Amphenol Communications Solutions (FCI).
- USB 2.0, one-port, 16 terminal contact positions, 0.50 mm pitch, right-angle
  top-mount SMT with through-hole shell stakes; 5 A total VBUS/GND rating,
  1.25 A CC rating, 10,000 mating cycles, IR reflow, 0.60 mm recommended PCB.
- Manufacturer drawing supplies the pad layout, shell geometry, pin assignment,
  and 6.5 mm connector length. The local derived pattern has 16 contact pads
  plus two shell pads and retains the source coordinate families.

## Procurement evidence

The manufacturer lists the part Active and Stocked, with cut tape MOQ 1 at
about $0.79 and tape/reel break quantity 1,200. The same manufacturer page
reported distributor stock of Mouser 12,763, DigiKey 4,688, Newark 1,180,
Arrow 935, and Farnell 20 in its 2026-08-30 capture. DigiKey reported 4,316
in stock, active status, 18-week manufacturer lead, cut tape/Digi-Reel, and
about $0.79 quantity 1; Newark reported cut tape MOQ 1 at about $0.85 and
full-reel MOQ 12,000. Mouser and Arrow expose the exact MPN and ECAD/drawing
records. LCSC has an exact listing, but no dependable stock/assembly snapshot
was used as the closure basis.

Sourcing risk: `LOW`. Multiple reputable distributors, MOQ 1, ordinary SMT
assembly, and a compatible parametric substitute are available. Full-reel
factory pack is 12,000 but does not constrain prototype procurement.

## Local reference and provenance

- `../../../../footprints/PiSXMe.pretty/USB_C_SERVICE_10171746.kicad_mod` is the
  pre-existing project reference; the clean copy is generated into
  `PiSXMe_RevA_Clean.pretty/USB_C_SERVICE_10171746.kicad_mod`.
- Manufacturer drawing: `https://cdn.amphenol-cs.com/media/wysiwyg/files/drawing/10171746.pdf`.
- Product page: `https://www.amphenol-cs.com/product/1017174600021lf.html`.
- The drawing and model remain manufacturer copyrighted. The repository keeps
  a derived footprint and source metadata, not a redistributed manufacturer CAD
  package.

## Exact PiSXMe decision closed

The Phase 8 generic `USB2_UFP_CONNECTOR` placeholder is replaced by the
documented Amphenol `10171746-00021LF`; SERVICE now carries the exact MPN and
clean-library footprint assignment. Its USB2-only contract remains unchanged.
