nova-rey/pisxme/pisxme/reva-clean/authority-inventory/primary-docs/storage-upgrade/connectors/te/TE_MKEY_AUTHORITY.md

# TE M-key Socket 3 authority

Candidate: `1-2199230-4`, TE Connectivity 67-position, 0.5-mm pitch, 4.2-mm
height, right-angle SMT, M code, gold contact finish.

## Manufacturer evidence

TE's exact product page identifies the part as Active, M code, 67 positions,
SMT, 4.2 mm height, 50 VAC and 0.5 A per contact, with customer 2D/3D CAD
links and application specification `114-115006`:

https://www.te.com/de/product-1-2199230-4.html

The retained LCSC datasheet is a procurement corroboration only. TE's
application specification is captured at:

https://www.te.com/commerce/DocumentDelivery/DDEController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

Local file: `TE-114-115006-application-spec-revC.pdf`.

The application spec states that the M.2 connector accepts standard modules,
is designed for automatic placement, requires precisely located PCB pads,
and gives reflow, insertion and removal guidance. The exact TE customer 2D
CAD is now captured as `cad/TE-1-2199230-4-2d-dxf.zip`; the application
specification Figure 2 is retained as the PCB pad-layout authority. A KiCad
footprint still needs to be authored and pad-by-pad checked before production
replacement.

## Procurement and decision

DigiKey carries the exact MPN with MOQ 1 and a displayed quantity-1 price of
approximately $2.11 in the captured page, but the page showed factory lead
time rather than dependable immediate stock. TE's page currently says the
part is not available and directs buyers to TE/distributor support. Sourcing
risk is MEDIUM. The exact MPN is preferable to the existing JAE B-key part,
but it is not production-closed until the customer drawing/CAD and a current
prototype quote are retained.

Decision: replace the existing B-key J3 only after exact M-key contact/pad
mapping, 2280 retention geometry, courtyard, and procurement checks pass.

## Provenance

TE material is retained as manufacturer reference documentation. The LCSC
copy is labeled corroborating procurement evidence and is not used as the
land-pattern authority.
