nova-rey/pisxme/pisxme/reva-clean/authority-inventory/primary-docs/ethernet-magjack/EDAC_A70-112-331N126_SOURCE_RECEIPT.md

# EDAC A70-112-331N126 source receipt

Capture date: 2026-08-30

Authoritative drawing (EDAC drawing served through Mouser):
`https://www.mouser.com/catalog/specsheets/EDAC_A70-112-331N126.pdf`

Exact distributor record:
`https://www.mouser.com/en/ProductDetail/EDAC/A70-112-331N126?qs=3vio67wFuYr/LpvF4Nvj2w%3D%3D`

Manufacturer family/catalog authority: `https://edac.net/products`

Backup manufacturer/distributor path: `https://www.l-p.com/products/432379.htm`

Original reference manufacturer page: `https://www.trxcom.com/products/203.html`

The exact drawing was opened as a five-page PDF. Its title block identifies
EDAC Inc. and part `A70-112-331N126`; the drawing revision history includes a
July 2024 update. The Mouser CDN did not complete a local binary download in
this environment, so this receipt stores source metadata and derived facts;
the manufacturer drawing remains authoritative. Phase 3 must reproduce its
recommended layout and save a generated footprint plus pad/hole comparison.
