nova-rey/pisxme/pisxme/reva-clean/validation/phase3/PHASE3_EXIT_RECEIPT.md

# PiSXMe Rev A Clean — Phase 3 exit receipt

Checked: 2026-08-30. Status: `PISXME_REVA_CLEAN_PHASE3_CLOSED`.

| Check | Result | Evidence |
|---|---|---|
| Native KiCad reopen and hierarchy | PASS | `test_native_hierarchy_authoring.py`; all ten child sheets load and root/child association is native |
| Native ERC | PASS | KiCad 10.0.5: `Found 0 violations` |
| Netlist export | PASS | non-empty `PiSXMe_RevA_Clean.xml`; ten uniquely referenced child-sheet contract components |
| Clean namespace/path scan | PASS | zero `PiSXMe:` IDs and zero absolute model/source paths in clean KiCad source |
| CM5 symbol/pad parity | PASS | 200 electrical symbol pins = 200 footprint pads |
| EDAC symbol/pad parity | PASS | `A70-112-331N126`: P1–P18 = 18 pins/pads; shield is mechanical NPTH, not an electrical pad |
| Schematic↔PCB parity fixture | PASS | `test_schematic_pcb_parity.py` parses the native-format disposable fixture and proves PCB-only/proxy nets = 0; native KiCad DRC reports 0 violations |

The clean architecture has no production PCB yet, as required by the
placement/routing boundary. The disposable native-format fixture supplies the
missing positive parity test without introducing a clean PCB artifact or
silently treating an empty set as sufficient evidence.

The authoring regression regenerates the hierarchy, checks that the contract
symbol is inside each child `lib_symbols` expression, checks native
sheet-instance serialization, and runs native ERC. The generic defect was a
contract symbol appended after `lib_symbols` plus an inverted library-pin Y
coordinate; the authoring path now fixes both, emits real root wires, and
assigns deterministic child contract references.

This closes Phase 3 schematic architecture and library isolation only. No
placement, routing, fabricated-hardware, Linux bridge, SI, PI, thermal, or
mechanical-fit claim is made here. Phase 4 may begin with the approved V100
lane-0 schematic transplant; PCB placement/routing remain later phases.
