nova-rey/pisxme/pisxme/reva-clean/validation/phase3/PHASE3_SCAFFOLD_RECEIPT.md

# Phase 3 scaffold receipt

Checked: 2026-08-30.

The native root and ten child schematic files are present and plot/reopen
through KiCad 10.0.5 under `xvfb-run`. Root sheet count is 10 and the clean
source contains no legacy `PiSXMe:` identifiers or machine-local paths outside
the preserved authority/donor evidence. The root schematic is generated by
`phase3_scaffold.py` from the local disposable SKiDL hierarchy fixture; the
generator is deterministic and contains no production connectivity.

Hierarchy gate: `PISXME_REVA_CLEAN_PHASE3_HIERARCHY_CLOSED`.

The child sheets contain native `PiSXMeRevAClean` contract symbols with passive
pins wired to every hierarchical interface label. The generic authoring path
now places those definitions inside each child `lib_symbols` section, negates
library-pin row Y coordinates, and generates root wires to every sheet pin.
KiCad 10.0.5 root ERC reports zero violations across all ten children. The
regression is covered by `test_native_hierarchy_authoring.py`. No production
placement or routing was introduced.

Native control evidence: the installed KiCad `video` multi-sheet demo also
reopens and passes native ERC with zero violations. The clean root and child
files now match the relevant native loading and connectivity behavior.

The Phase 3 exit gate is closed. Production asset extraction and
machine-readable pin/pad parity are recorded by
`validate_local_assets.py`: CM5 200/200 and EDAC `A70-112-331N126` 18/18.
There is intentionally no clean PCB yet because placement and routing are
prohibited through the architecture gate; PCB-only/proxy-net parity is
therefore a zero-net construction check at this gate.
