nova-rey/pisxme/pisxme/reva-clean/authority-inventory/primary-docs/m2-jse/TE-2199119-family-drawing.pdf

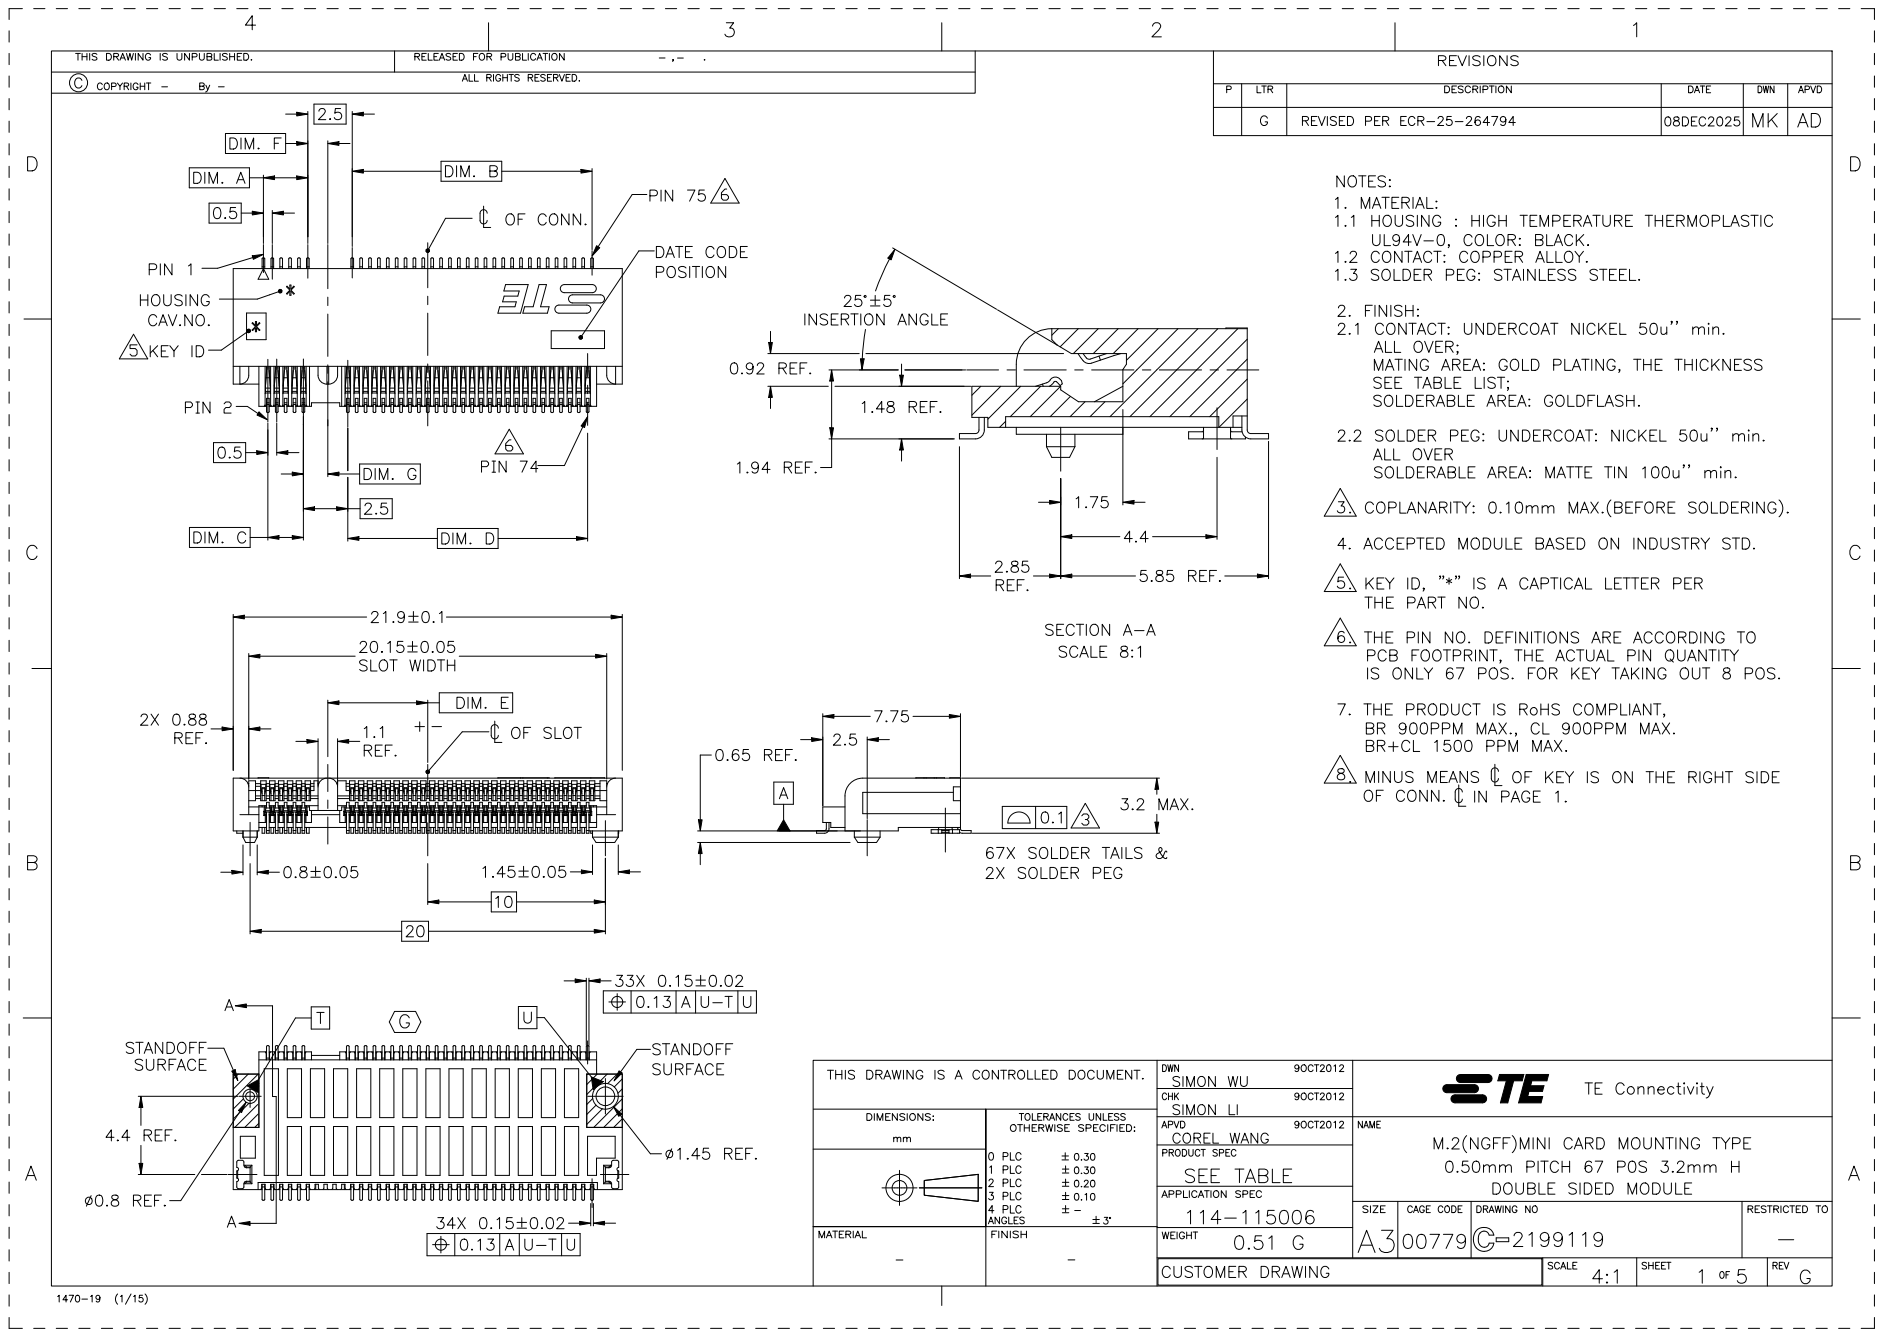
[picture p6: page 1]

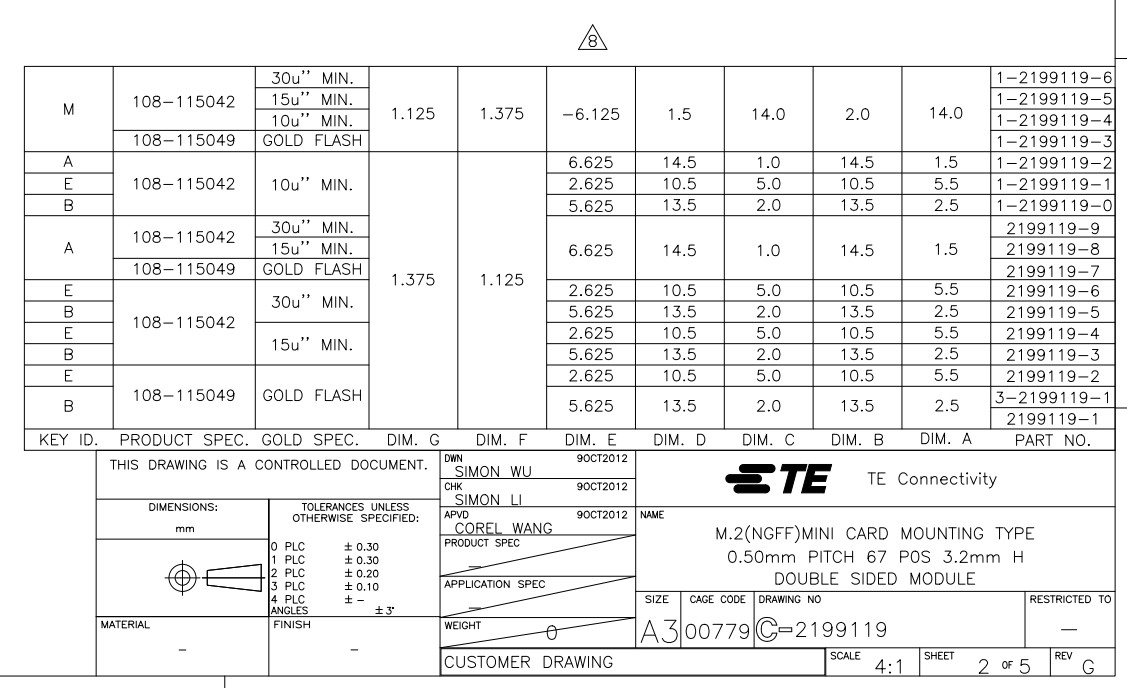
[picture p7: page 2]

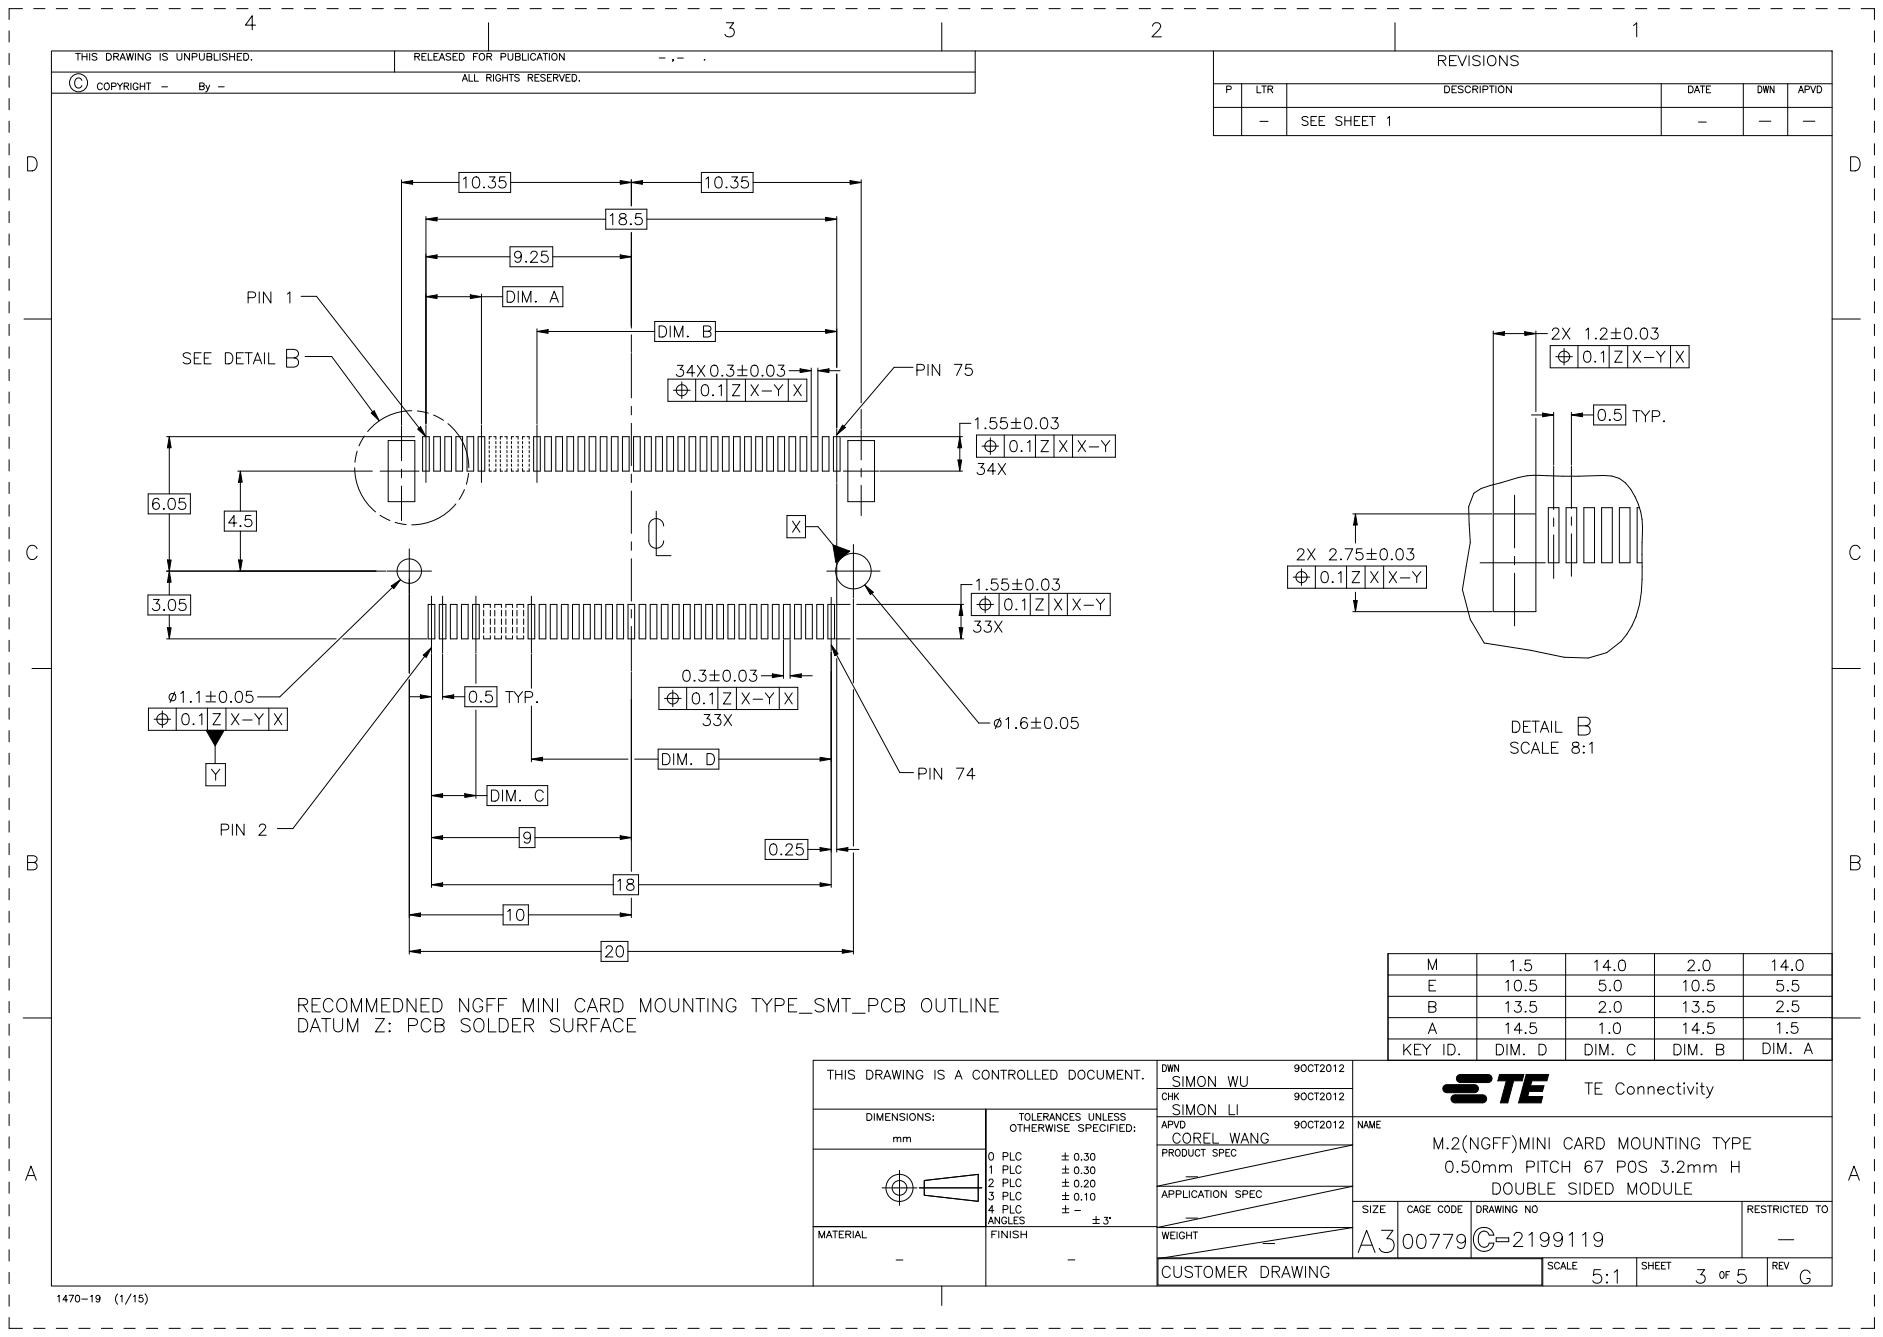
[picture p8: page 3]

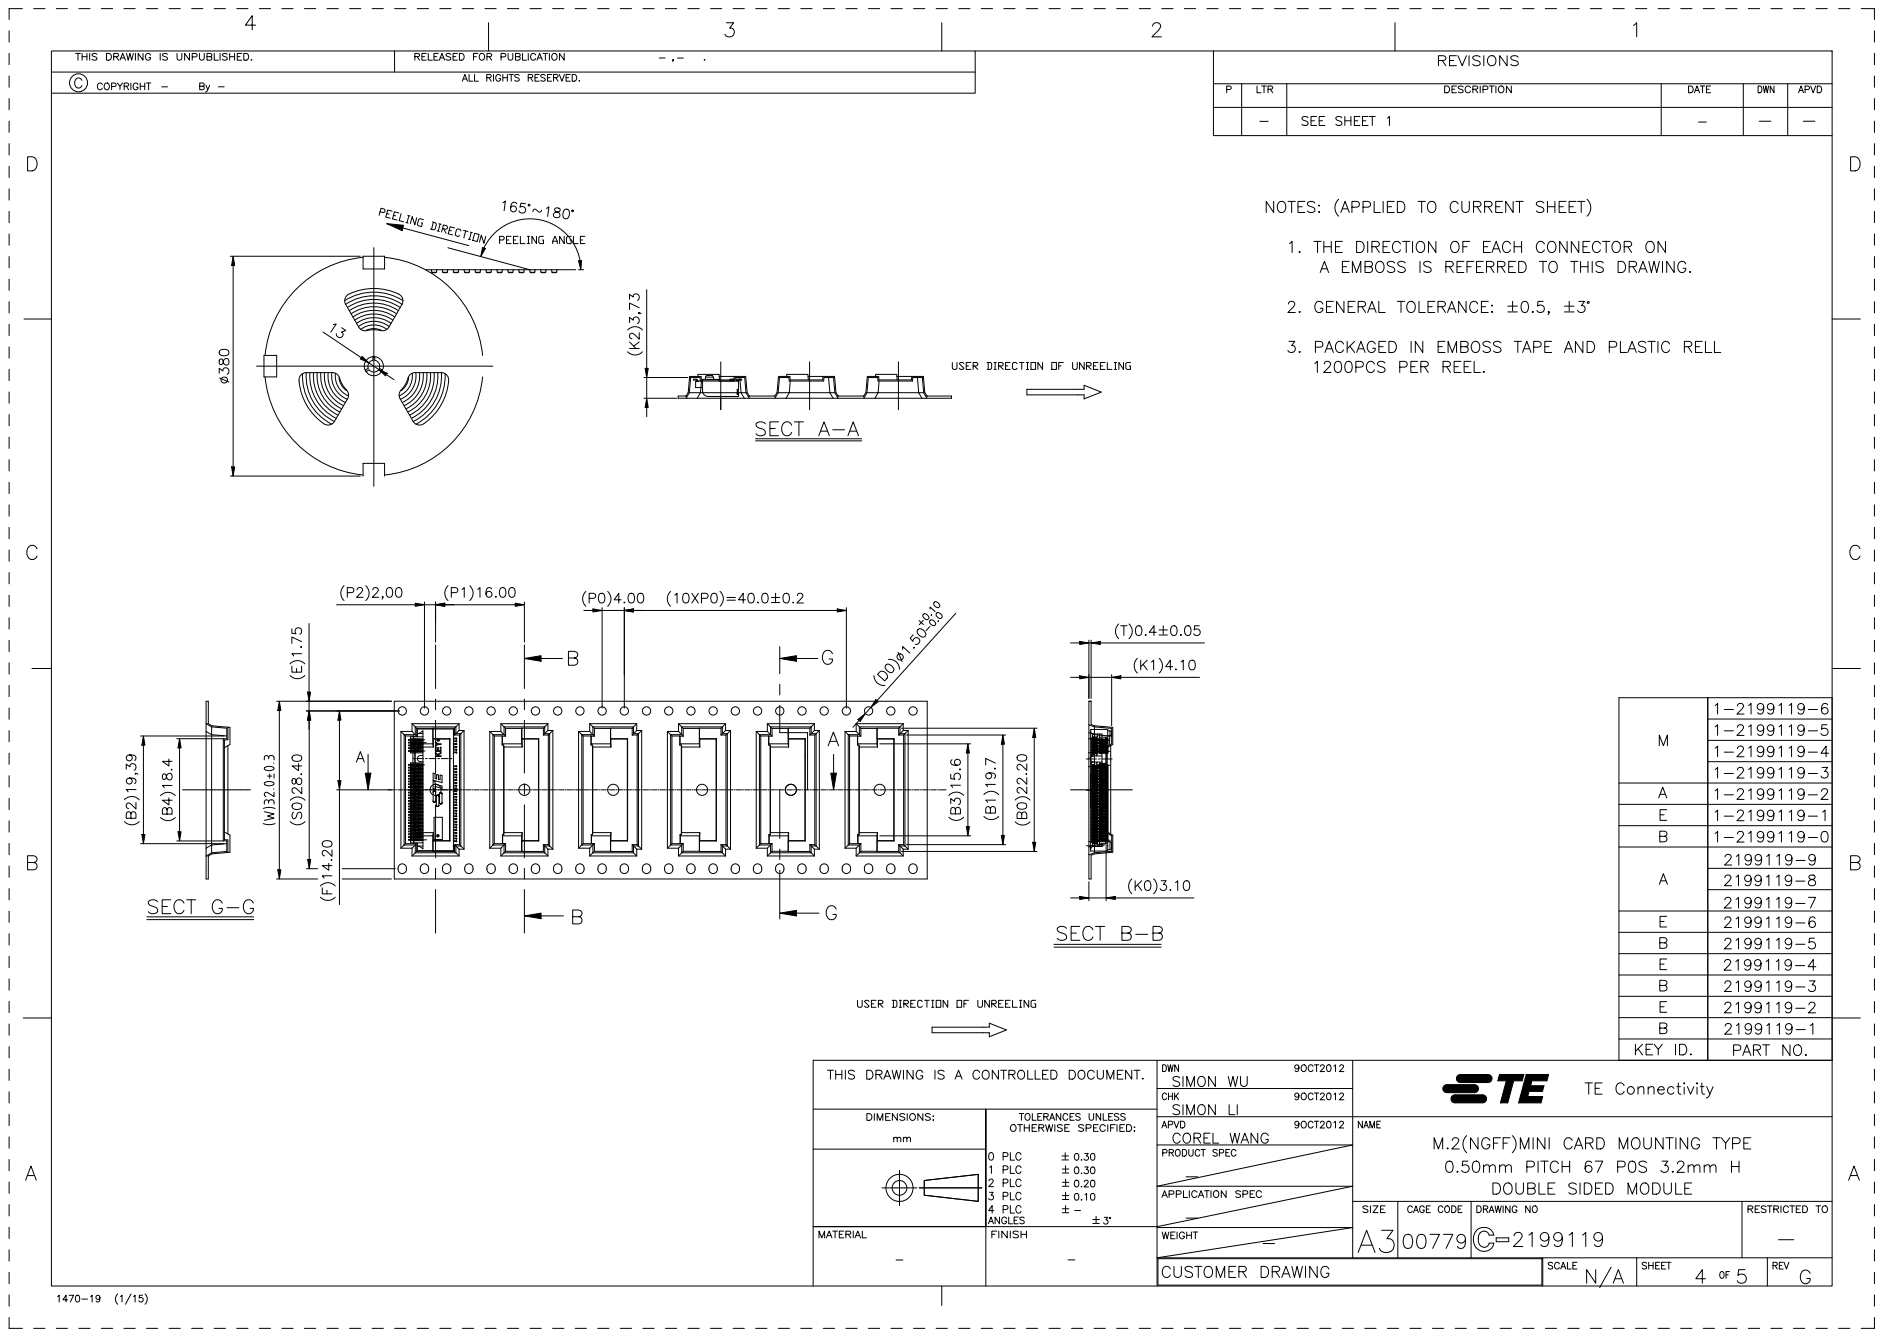
[picture p9: page 4]

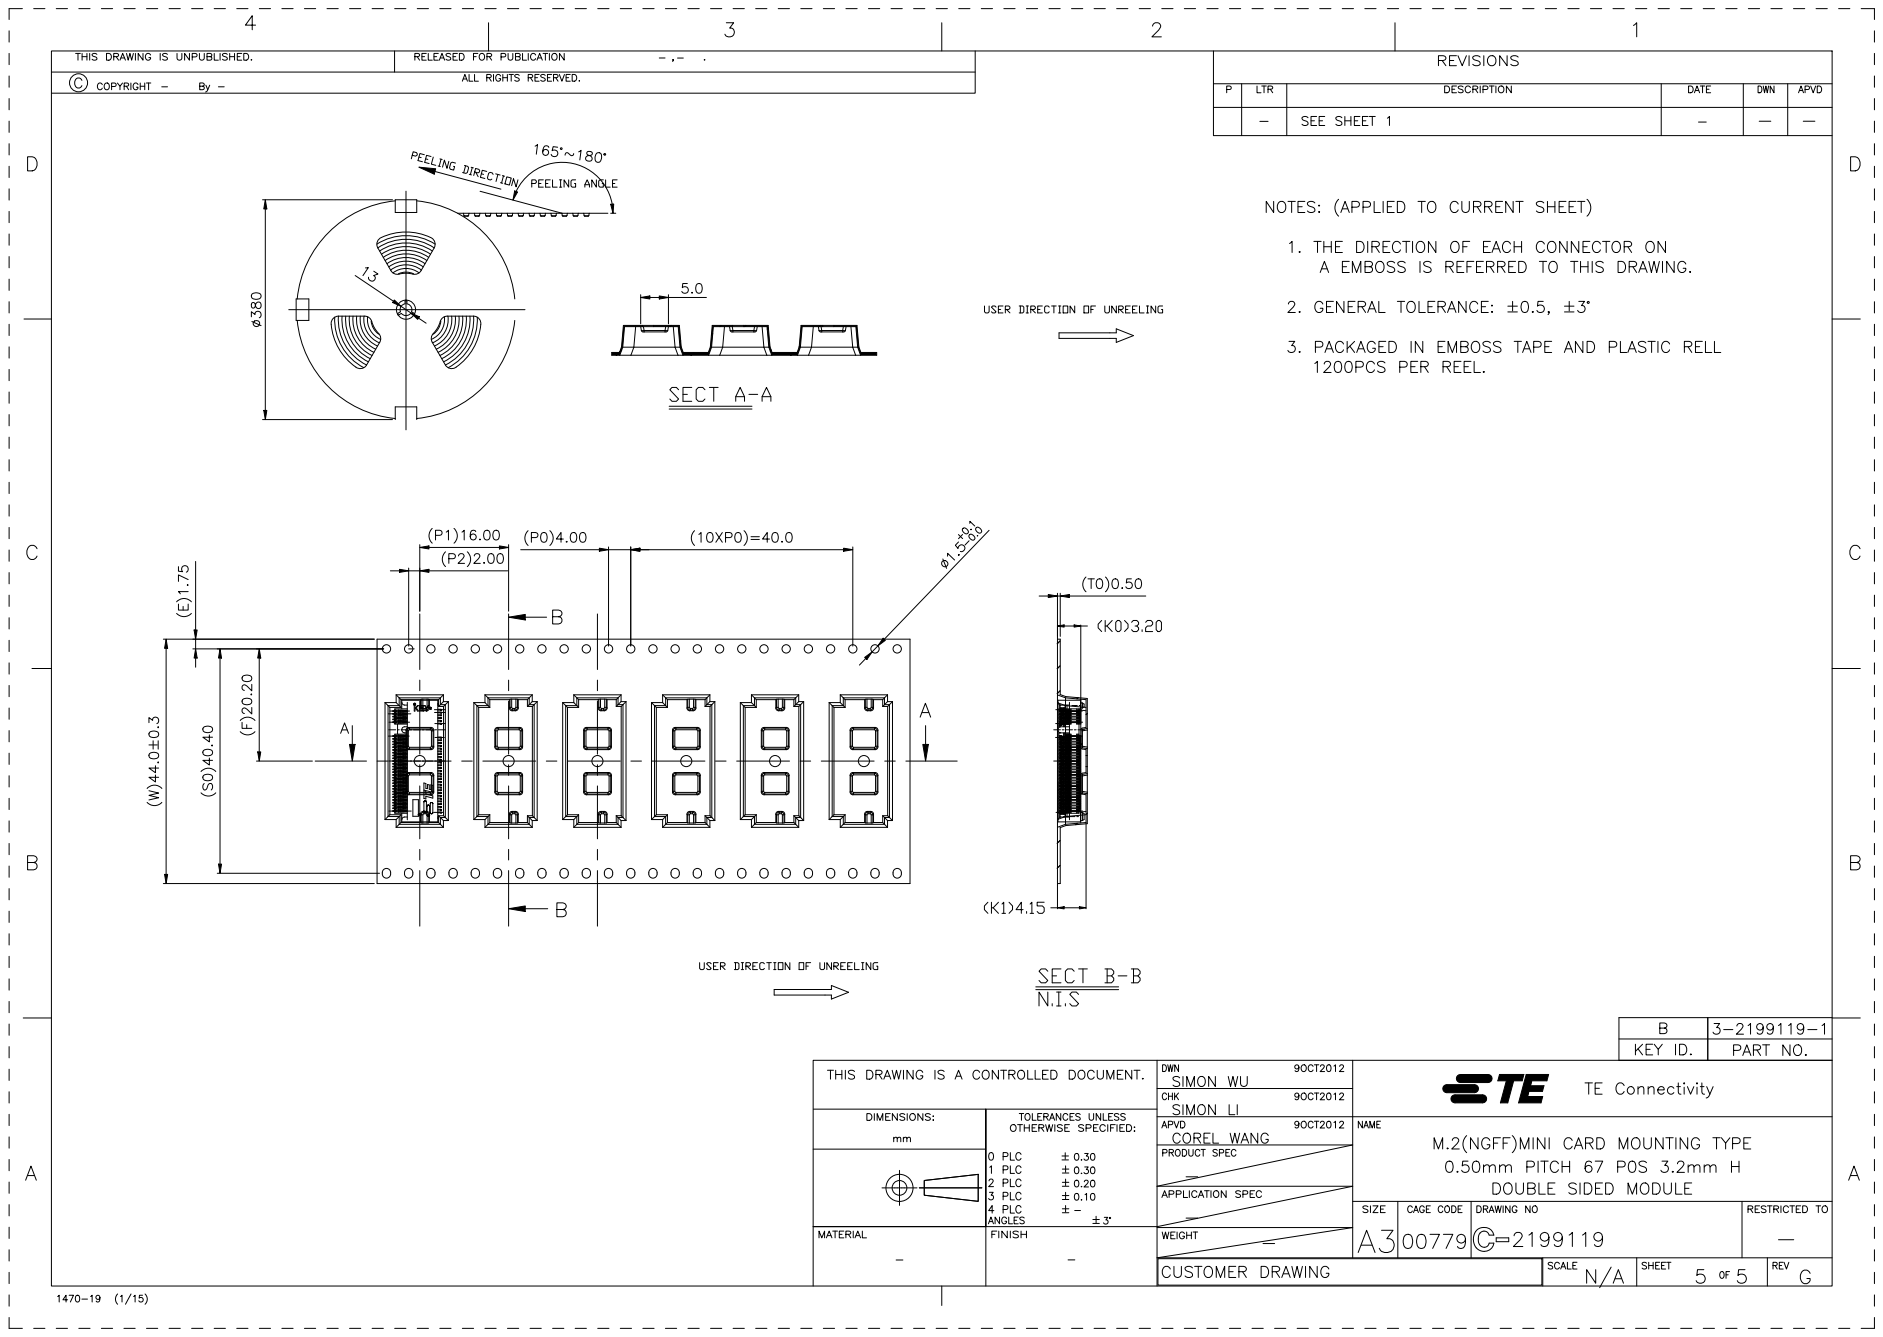
[picture p10: page 5]
