nova-rey/pisxme/pisxme/reva-clean/authority-inventory/rtl9210b/community-lz1/root-reference/M.2_0.kicad_sch

## KiCad design pisxme/reva-clean/authority-inventory/rtl9210b/community-lz1/root-reference/M.2_0.kicad_sch (2026-09-06)

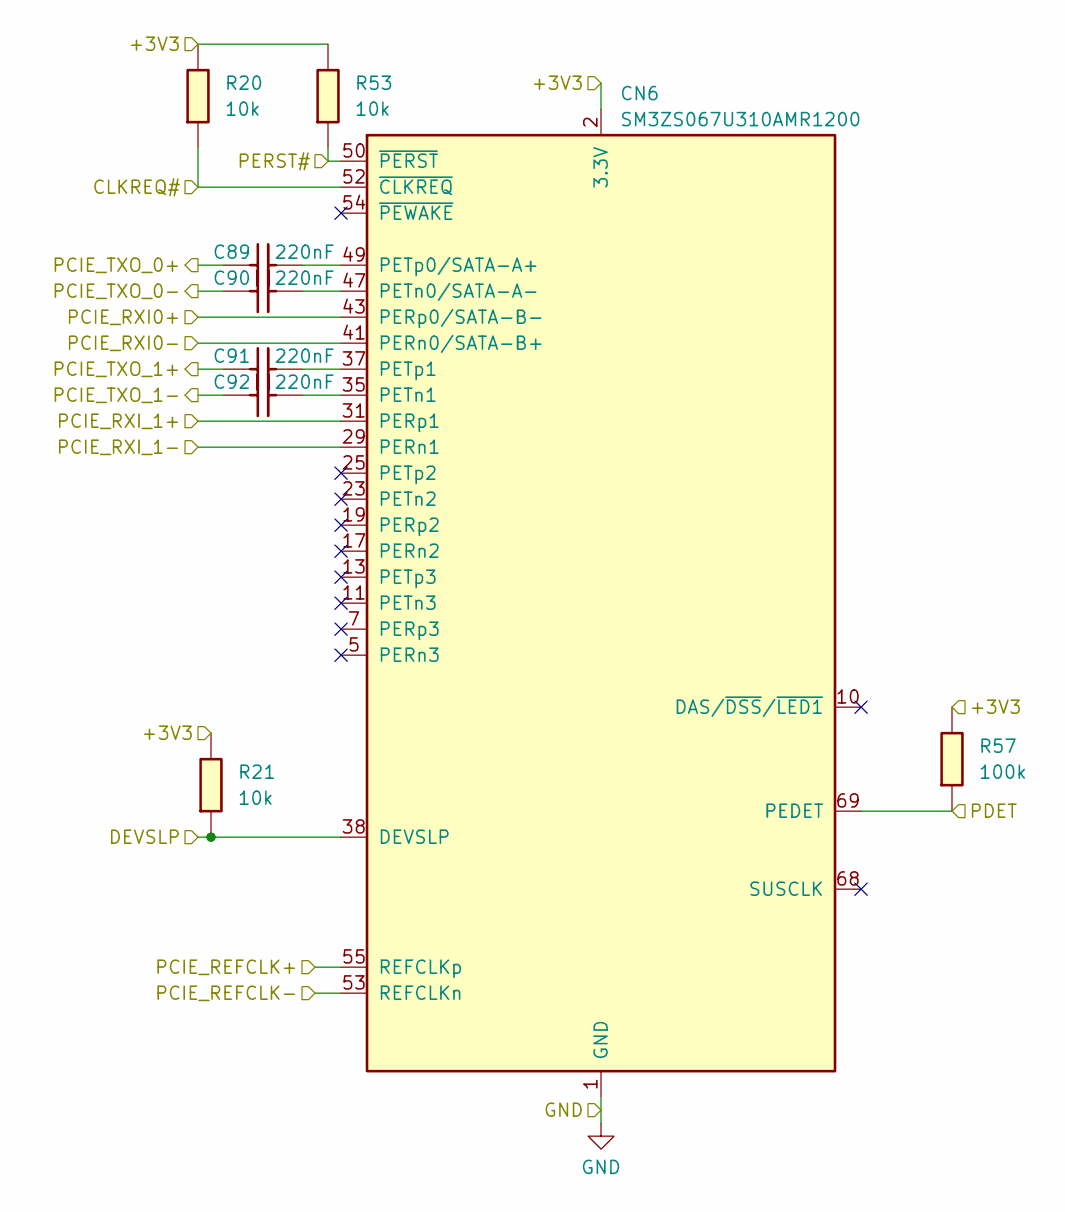
[picture p22: schematic M.2_0.kicad_sch]

Parts:
C89, C90, C91, C92: 220nF; C_0402_1005Metric; Manufacturer Part CL05B224KO5NNNC; LCSC C16772
CN6: SM3ZS067U310AMR1200; 2E0BC21-S85BM-7H; Manufacturer Part SM3ZS067U310AMR1200; LCSC C4527433
R20, R21, R53: 10k; R_0402_1005Metric; Manufacturer Part 0402WGF1002TCE; LCSC C25744
R57: 100k; R_0402_1005Metric; Manufacturer Part 0402WGF1003TCE; LCSC C25741

Connections:
+3V3: CN6.2 (3.3V), CN6.4 (3.3V), CN6.12 (3.3V), CN6.14 (3.3V), CN6.16 (3.3V), CN6.18 (3.3V), CN6.70 (3.3V), CN6.72 (3.3V), CN6.74 (3.3V), R20.2, R21.2, R53.2, R57.2
CLKREQ#: CN6.52 (~CLKREQ), R20.1
DEVSLP: CN6.38 (DEVSLP), R21.1
GND: CN6.1 (GND), CN6.3 (GND), CN6.9 (GND), CN6.15 (GND), CN6.21 (GND), CN6.27 (GND), CN6.33 (GND), CN6.39 (GND), CN6.45 (GND), CN6.51 (GND), CN6.57 (GND), CN6.71 (GND), CN6.73 (GND), CN6.75 (GND)
unnamed: C89.2, CN6.49 (PETp0/SATA-A+)
unnamed: C90.2, CN6.47 (PETn0/SATA-A-)
unnamed: C91.2, CN6.37 (PETp1)
unnamed: C92.2, CN6.35 (PETn1)
PCIE_REFCLK+: CN6.55 (REFCLKp)
PCIE_REFCLK-: CN6.53 (REFCLKn)
PCIE_RXI0+: CN6.43 (PERp0/SATA-B-)
PCIE_RXI0-: CN6.41 (PERn0/SATA-B+)
PCIE_RXI_1+: CN6.31 (PERp1)
PCIE_RXI_1-: CN6.29 (PERn1)
PCIE_TXO_0+: C89.1
PCIE_TXO_0-: C90.1
PCIE_TXO_1+: C91.1
PCIE_TXO_1-: C92.1
PDET: CN6.69 (PEDET), R57.1
PERST#: CN6.50 (~PERST), R53.1
