nova-rey/pisxme/pisxme/reva-clean/phase19_live_coordinated_open_island.py

"""Phase 19 disposable candidate using reloaded U7/J3/clock endpoints.

This is deliberately an acreage experiment.  No inherited USB3/SATA/clock
copper is retained; the source CM5 pads, bridge, socket, split caps, and
40-MHz clock are regenerated as one coordinated island.
"""
from pathlib import Path
import os, re, pcbnew
R=Path(__file__).resolve().parent
ARGS={}
for _arg in __import__('sys').argv[1:]:
 if _arg.startswith('--') and '=' in _arg:
  _k,_v=_arg[2:].split('=',1); ARGS[_k]=_v
BASE=R/ARGS.get('P19_BASE',os.environ.get('P19_BASE','ACREAGE_CLOCK_CANDIDATE5.kicad_pcb'))
SYNC=R/'.phase19_open_island_sync.kicad_pcb'
OUT=R/'PHASE19_OPEN_ISLAND_LIVE.kicad_pcb'
PREP=ARGS.get('P19_PREP',os.environ.get('P19_PREP','0'))=='1'
SKIP_SATA=ARGS.get('P19_SKIP_SATA',os.environ.get('P19_SKIP_SATA','0'))=='1'
SKIP_CLOCK=ARGS.get('P19_SKIP_CLOCK',os.environ.get('P19_SKIP_CLOCK','0'))=='1'
SKIP_USB=ARGS.get('P19_SKIP_USB',os.environ.get('P19_SKIP_USB','0'))=='1'
CLOCK_ONLY=ARGS.get('P19_CLOCK_ONLY',os.environ.get('P19_CLOCK_ONLY','0'))=='1'
SATA270=ARGS.get('P19_SATA270',os.environ.get('P19_SATA270','0'))=='1'
USB_EAST=ARGS.get('P19_USB_EAST',os.environ.get('P19_USB_EAST','0'))=='1'
USB_TOP_EAST=ARGS.get('P19_USB_TOP_EAST',os.environ.get('P19_USB_TOP_EAST','0'))=='1'
USB_PAIR_SPLIT=ARGS.get('P19_USB_PAIR_SPLIT',os.environ.get('P19_USB_PAIR_SPLIT','0'))=='1'
USB_VERTICAL=ARGS.get('P19_USB_VERTICAL',os.environ.get('P19_USB_VERTICAL','0'))=='1'
USB_ORDERED=ARGS.get('P19_USB_ORDERED',os.environ.get('P19_USB_ORDERED','0'))=='1'
USB_ORDERED_ORACLE=ARGS.get('P19_USB_ORDERED_ORACLE',os.environ.get('P19_USB_ORDERED_ORACLE','0'))=='1'
USB_WIDE=ARGS.get('P19_USB_WIDE',os.environ.get('P19_USB_WIDE','0'))=='1'
USB_SPLIT=ARGS.get('P19_USB_SPLIT',os.environ.get('P19_USB_SPLIT','0'))=='1'
KEEP_STORAGE=ARGS.get('P19_KEEP_STORAGE',os.environ.get('P19_KEEP_STORAGE','0'))=='1'
U7ROT=int(ARGS.get('P19_U7_ROT',os.environ.get('P19_U7_ROT','270')))
U7X=float(ARGS.get('P19_U7_X',os.environ.get('P19_U7_X','280')))
U7Y=float(ARGS.get('P19_U7_Y',os.environ.get('P19_U7_Y','105')))
J3X=float(ARGS.get('P19_J3_X',os.environ.get('P19_J3_X','200')))
J3Y=float(ARGS.get('P19_J3_Y',os.environ.get('P19_J3_Y','140')))
RELOCATED=abs(U7X-280.0)>0.01 or abs(U7Y-105.0)>0.01 or abs(J3X-200.0)>0.01 or abs(J3Y-140.0)>0.01
def C(x,y): return (x+(U7X-280.0), y+(U7Y-105.0)-30.0)
def CY(y): return y+(U7Y-105.0)-30.0
W=pcbnew.FromMM(.200)
def V(x,y): return pcbnew.VECTOR2I_MM(x,y)
def pos(p): return (pcbnew.ToMM(p.GetPosition().x),pcbnew.ToMM(p.GetPosition().y))
def pad(f,n): return next(p for p in f.Pads() if str(p.GetNumber())==str(n))
def net(b,name):
 aliases={'/CORE_CM5/CM5_USB3_RX_N':'CM5_USB3_RX_N','/CORE_CM5/CM5_USB3_RX_P':'CM5_USB3_RX_P','/CORE_CM5/CM5_USB3_TX_N':'CM5_USB3_TX_N','/CORE_CM5/CM5_USB3_TX_P':'CM5_USB3_TX_P'}
 n=b.FindNet(name)
 if n is None and name in aliases: n=b.FindNet(aliases[name])
 if n is None:
  n=pcbnew.NETINFO_ITEM(b,name); n.SetNetCode(b.GetNetCount()+1); b.Add(n)
 return n
def seg(b,n,a,z,layer=pcbnew.F_Cu,width=W):
 if a == z: return
 t=pcbnew.PCB_TRACK(b); t.SetStart(V(*a)); t.SetEnd(V(*z)); t.SetLayer(layer); t.SetWidth(width); t.SetNet(n); b.Add(t)
def via(b,n,p):
 q=pcbnew.PCB_VIA(b); q.SetPosition(V(*p)); q.SetWidth(pcbnew.FromMM(.50)); q.SetDrill(pcbnew.FromMM(.30)); q.SetLayerPair(pcbnew.F_Cu,pcbnew.B_Cu); q.SetNet(n); b.Add(q)
def via_sig(b,n,p):
 # The board contract permits ordinary through-vias only; keep the signal
 # helper inside the native 0.30 mm minimum finished-drill rule.
 q=pcbnew.PCB_VIA(b); q.SetPosition(V(*p)); q.SetWidth(pcbnew.FromMM(.50)); q.SetDrill(pcbnew.FromMM(.30)); q.SetLayerPair(pcbnew.F_Cu,pcbnew.B_Cu); q.SetNet(n); b.Add(q)
def strip_old(b):
 for t in list(b.GetTracks()):
  n=t.GetNetname()
  targets=('CM5_USB3',) if KEEP_STORAGE else ('CM5_USB3','BRIDGE_SATA','SATA_M2','BRIDGE_XI','BRIDGE_XO','BRIDGE_VSSOSC','BRIDGE_3V3')
  if any(x in n for x in targets):
   b.Remove(t)
def setpad(p,n): p.SetNet(n); p.SetNetCode(n.GetNetCode())
def main():
 if PREP:
  b=pcbnew.LoadBoard(str(BASE))
  u=b.FindFootprintByReference('U7'); j=b.FindFootprintByReference('J3')
  # Open region to the right of the PCIe/CM5 source corridors.
  u.SetPosition(V(U7X,U7Y)); u.SetOrientationDegrees(U7ROT)
  j.SetPosition(V(J3X,J3Y)); j.SetOrientationDegrees(270 if SATA270 else 90)
  old_mech=b.FindFootprintByReference('MECH_M2_2280')
  if old_mech is not None and not KEEP_STORAGE: b.Remove(old_mech)
  # This donor already carries clean C30-C33 clock-candidate objects.
  _caps=({'C30':(U7X-40,U7Y+5),'C31':(U7X-40,U7Y+3),'C32':(U7X-40,U7Y+9),'C33':(U7X-40,U7Y+7)} if SATA270 else {'C30':(U7X-15,U7Y-9),'C31':(U7X-15,U7Y-5),'C32':(U7X-15,U7Y+3),'C33':(U7X-15,U7Y+7)})
  if not KEEP_STORAGE:
   for ref,(x,y) in _caps.items():
    f=b.FindFootprintByReference(ref); f.SetPosition(V(x,y)); f.SetOrientationDegrees(0 if SATA270 else 180)
  # Put the low-profile clock island in open south acreage, clear of the
  # relocated U7/SATA launch.  The placement remains relative to U7/J3.
  if not KEEP_STORAGE:
   for ref,xyv in {'Y1':(U7X-120,U7Y-45),'R23':(U7X-116,U7Y-45),'C42':(U7X-116,U7Y-49),'C43':(U7X-112,U7Y-45)}.items():
    f=b.FindFootprintByReference(ref)
    if f is None: raise RuntimeError('clock donor missing '+ref)
    f.SetPosition(V(*xyv)); f.SetOrientationDegrees(0)
  strip_old(b); b.Save(str(SYNC)); print(SYNC); return
 b=pcbnew.LoadBoard(str(SYNC))
 caps={ref:b.FindFootprintByReference(ref) for ref in ('C30','C31','C32','C33')}
 caps={ref:b.FindFootprintByReference(ref) for ref in ('C30','C31','C32','C33')}
 # All endpoints below are obtained only after native serialization reload.
 u=b.FindFootprintByReference('U7'); j=b.FindFootprintByReference('J3'); src=b.FindFootprintByReference('J7')
 U={str(p.GetNumber()):pos(p) for p in u.Pads()}; J={str(p.GetNumber()):pos(p) for p in j.Pads()}; S={str(p.GetNumber()):pos(p) for p in src.Pads()}
 N={}
 for name in ('/CORE_CM5/CM5_USB3_RX_N','/CORE_CM5/CM5_USB3_RX_P','/CORE_CM5/CM5_USB3_TX_N','/CORE_CM5/CM5_USB3_TX_P',
              '/STORAGE/BRIDGE_SATA_TX_P','/STORAGE/BRIDGE_SATA_TX_N','/STORAGE/BRIDGE_SATA_RX_P','/STORAGE/BRIDGE_SATA_RX_N',
              '/STORAGE/SATA_M2_TX_P','/STORAGE/SATA_M2_TX_N','/STORAGE/SATA_M2_RX_P','/STORAGE/SATA_M2_RX_N',
              '/STORAGE/BRIDGE_XI','/STORAGE/BRIDGE_XO','/STORAGE/BRIDGE_VSSOSC'):
  N[name]=net(b,name)
 # USB3: source fanout drops to parallel B.Cu corridors below the PCIe bbox,
 # then climbs only in the open x>190 region and returns on F.Cu at U7.
 usb=(('CM5_USB3_RX_N','128','42',(78,90),(260,90)),('CM5_USB3_RX_P','130','43',(76,92),(265,92)),
      ('CM5_USB3_TX_N','140','45',(74,94),(270,94)),('CM5_USB3_TX_P','142','46',(72,96),(275,96))) if USB_EAST else (('CM5_USB3_RX_N','128','42',(78,114),(200,114)),('CM5_USB3_RX_P','130','43',(76,116),(204,116)),
      ('CM5_USB3_TX_N','140','45',(74,118),(208,118)),('CM5_USB3_TX_P','142','46',(72,120),(212,120)))
 for suffix,sp,up,start,far in usb:
  if SKIP_USB:
   continue
  n=N['/CORE_CM5/'+suffix]; s=S[sp]; d=U[up]
  setpad(pad(src,sp),n); setpad(pad(u,up),n)
  if (USB_ORDERED or USB_SPLIT) and U7ROT == 270:
    # Source-order monotonic escape: J7 pads serialize RX_N, RX_P, TX_N,
    # TX_P from low to high y.  Preserve that order through the initial
    # breakout, then use separated pair corridors and serialized U7 pad x.
    if USB_WIDE:
     # Wide-acreage split: keep the RX pair on an upper B.Cu lane and TX on
     # a lower F.Cu lane.  Both pairs approach the U7 USB edge from outside
     # the SATA launch, so the USB/SATA pad fields do not share a corridor.
     wide={
      'CM5_USB3_RX_N':((74.0,70.0),(276.0,70.0),(276.0,108.0),(276.0,108.0)),
      'CM5_USB3_RX_P':((84.0,72.0),(278.0,72.0),(278.0,106.0),(278.0,106.0)),
      'CM5_USB3_TX_N':((90.0,150.0),(280.0,150.0),(280.0,104.0),(280.0,104.0)),
      'CM5_USB3_TX_P':((86.0,152.0),(282.0,152.0),(282.0,102.0),(282.0,102.0))}
     launch=(71.2,s[1]); seg(b,n,s,launch)
     first={'CM5_USB3_RX_N':(74.0,103.9),'CM5_USB3_RX_P':(84.0,104.3),
            'CM5_USB3_TX_N':(90.0,106.3),'CM5_USB3_TX_P':(86.0,106.7)}[suffix]
     seg(b,n,launch,first,pcbnew.F_Cu); seg(b,n,first,wide[suffix][0],pcbnew.F_Cu)
     if suffix.startswith('CM5_USB3_RX_'):
      via(b,n,wide[suffix][0]); layer=pcbnew.B_Cu
     else: layer=pcbnew.F_Cu
     seg(b,n,wide[suffix][0],wide[suffix][1],layer)
     seg(b,n,wide[suffix][1],wide[suffix][2],layer)
     if suffix.startswith('CM5_USB3_RX_'):
      via(b,n,wide[suffix][3]); seg(b,n,wide[suffix][3],d,pcbnew.F_Cu)
     else: seg(b,n,wide[suffix][3],d,pcbnew.F_Cu)
     continue
    if USB_ORDERED_ORACLE:
     # Transplant the proven ordered12 escape: preserve the CM5/J7-side
     # serialization exactly, translate only the U7-side x coordinates from
     # the old U7=(280,105) to the live U7=(270,105), and widen the two
     # final F.Cu dogbones around the ordinary 0.50/0.30-mm vias.
     oracle={
      'CM5_USB3_RX_N':([(74.0,80.0),(266.0,80.0),(266.0,108.0),(266.5,108.0)],(266.5,108.0)),
      'CM5_USB3_RX_P':([(84.0,82.0),(264.0,82.0),(264.0,106.0),(271.5,106.0)],(271.5,106.0)),
      'CM5_USB3_TX_N':([(90.0,118.0),(260.0,118.0),(260.0,104.0),(270.5,104.0)],(270.5,104.0)),
      'CM5_USB3_TX_P':([(86.0,120.0),(80.0,120.0),(80.0,102.0),(273.0,102.0)],(273.0,102.0))}
     launch=(71.2,s[1]); seg(b,n,s,launch)
     first={'CM5_USB3_RX_N':(74.0,103.9),'CM5_USB3_RX_P':(84.0,104.3),
            'CM5_USB3_TX_N':(90.0,106.3),'CM5_USB3_TX_P':(86.0,106.7)}[suffix]
     pre=first
     seg(b,n,launch,pre,pcbnew.F_Cu)
     if suffix in ('CM5_USB3_RX_N','CM5_USB3_RX_P','CM5_USB3_TX_N','CM5_USB3_TX_P'):
      if suffix == 'CM5_USB3_RX_N': seg(b,n,pre,(74.0,80.0),pcbnew.F_Cu)
      elif suffix == 'CM5_USB3_RX_P': seg(b,n,pre,(84.0,82.0),pcbnew.F_Cu)
      elif suffix == 'CM5_USB3_TX_N': seg(b,n,pre,(90.0,118.0),pcbnew.F_Cu)
      else: seg(b,n,pre,(86.0,120.0),pcbnew.F_Cu)
      via(b,n,oracle[suffix][0][0])
      pts=oracle[suffix][0]
      for a,z in zip(pts,pts[1:]): seg(b,n,a,z,pcbnew.B_Cu)
      via(b,n,oracle[suffix][1])
      seg(b,n,oracle[suffix][1],d,pcbnew.F_Cu)
     continue
    first={'CM5_USB3_RX_N':(74.0,103.9),'CM5_USB3_RX_P':(82.0,104.3),
           'CM5_USB3_TX_N':(90.0,118.0),'CM5_USB3_TX_P':(98.0,120.0)}[suffix]
    lane_y=({'CM5_USB3_RX_N':80.0,'CM5_USB3_RX_P':82.0,
             'CM5_USB3_TX_N':100.0,'CM5_USB3_TX_P':102.0} if RELOCATED else
            {'CM5_USB3_RX_N':50.0,'CM5_USB3_RX_P':52.0,
             'CM5_USB3_TX_N':90.0,'CM5_USB3_TX_P':92.0} if USB_SPLIT else
            {'CM5_USB3_RX_N':70.0,'CM5_USB3_RX_P':72.0,
             'CM5_USB3_TX_N':90.0,'CM5_USB3_TX_P':92.0})[suffix]
    ox=U7X-280.0
    target_x={'CM5_USB3_RX_N':(267.0 if RELOCATED else 280.0+ox),'CM5_USB3_RX_P':280.5+ox,
              'CM5_USB3_TX_N':(281.5+ox),'CM5_USB3_TX_P':282.0+ox}[suffix]
    landing_y={'CM5_USB3_RX_N':108.0,'CM5_USB3_RX_P':106.0,
               'CM5_USB3_TX_N':136.0,
               'CM5_USB3_TX_P':102.0}[suffix]
    trunk_x=({'CM5_USB3_RX_N':U7X+6.0,'CM5_USB3_RX_P':U7X+4.0,
             'CM5_USB3_TX_N':64.0,'CM5_USB3_TX_P':80.0} if RELOCATED else
             {'CM5_USB3_RX_N':290.0+ox,'CM5_USB3_RX_P':292.0+ox,
              'CM5_USB3_TX_N':294.0+ox,'CM5_USB3_TX_P':296.0+ox})[suffix]
    launch_x={'CM5_USB3_RX_N':71.2,'CM5_USB3_RX_P':72.2,
              'CM5_USB3_TX_N':71.2,'CM5_USB3_TX_P':72.2}[suffix]
    launch=(launch_x,s[1]); seg(b,n,s,launch)
    # Staircase source escape: each pre-via x is outside the preceding
    # vertical drop, so the serialized J7 fanout cannot self-cross.
    prex=({'CM5_USB3_RX_N':74.0,'CM5_USB3_RX_P':84.0,
           'CM5_USB3_TX_N':90.0,'CM5_USB3_TX_P':68.0} if RELOCATED else
          {'CM5_USB3_RX_N':74.0,'CM5_USB3_RX_P':84.0,
           'CM5_USB3_TX_N':90.0,'CM5_USB3_TX_P':68.0})[suffix]
    is_rx=suffix.startswith('CM5_USB3_RX_')
    seg(b,n,launch,(prex,s[1]),pcbnew.F_Cu)
    seg(b,n,(prex,s[1]),(prex,lane_y),pcbnew.F_Cu)
    if is_rx and RELOCATED and False:
     # Keep RX source corridors on B.Cu, but lift through an ordinary via
     # before the TX_N B.Cu trunk so the ordered lanes do not intersect.
     via_sig(b,n,(prex,lane_y)); seg(b,n,(prex,lane_y),(trunk_x,lane_y),pcbnew.B_Cu)
     rx_lift=(trunk_x,96.0); seg(b,n,(trunk_x,lane_y),rx_lift,pcbnew.B_Cu); via_sig(b,n,rx_lift)
     far_x=290.0 if suffix == 'CM5_USB3_RX_N' else 296.0
     corridor_y=94.0 if suffix == 'CM5_USB3_RX_N' else 90.0
     approach_y=116.0 if suffix == 'CM5_USB3_RX_N' else 112.0
     seg(b,n,rx_lift,(trunk_x,corridor_y),pcbnew.F_Cu)
     seg(b,n,(trunk_x,corridor_y),(far_x,corridor_y),pcbnew.F_Cu)
     seg(b,n,(far_x,corridor_y),(far_x,approach_y),pcbnew.F_Cu)
     if suffix == 'CM5_USB3_RX_N':
      seg(b,n,(far_x,approach_y),(270.0,approach_y),pcbnew.F_Cu); seg(b,n,(270.0,approach_y),(270.0,landing_y),pcbnew.F_Cu); seg(b,n,(270.0,landing_y),d,pcbnew.F_Cu)
     else:
      seg(b,n,(far_x,approach_y),(target_x,approach_y),pcbnew.F_Cu); seg(b,n,(target_x,approach_y),(target_x,landing_y),pcbnew.F_Cu); seg(b,n,(target_x,landing_y),d,pcbnew.F_Cu)
     continue
    if suffix == 'CM5_USB3_TX_N' and RELOCATED:
     # The relocated SATA RX_P launch occupies the lower B.Cu corridor.
     # Cross to F.Cu in open acreage before the final U7 approach.
     via_sig(b,n,(prex,lane_y))
     seg(b,n,(prex,lane_y),(trunk_x,lane_y),pcbnew.B_Cu)
     mid=(170.0,lane_y); seg(b,n,(trunk_x,lane_y),mid,pcbnew.B_Cu); via_sig(b,n,mid)
     # Go below the unpopulated lower half of the M.2 connector before
     # returning to the U7-side landing corridor.
     seg(b,n,mid,(mid[0],155.0),pcbnew.F_Cu)
     seg(b,n,(mid[0],155.0),(220.0,155.0),pcbnew.F_Cu)
     seg(b,n,(220.0,155.0),(220.0,landing_y),pcbnew.F_Cu)
     seg(b,n,(220.0,landing_y),(target_x,landing_y),pcbnew.F_Cu)
     seg(b,n,(target_x,landing_y),d,pcbnew.F_Cu)
     continue
    else:
     if (not USB_SPLIT) or (not is_rx): via_sig(b,n,(prex,lane_y))
     layer=pcbnew.F_Cu if (USB_SPLIT and is_rx) else pcbnew.B_Cu
     seg(b,n,(prex,lane_y),(trunk_x,lane_y),layer)
     seg(b,n,(trunk_x,lane_y),(trunk_x,landing_y),layer); seg(b,n,(trunk_x,landing_y),(target_x,landing_y),layer)
     if (not USB_SPLIT) or (not is_rx): via_sig(b,n,(target_x,landing_y))
    if suffix == 'CM5_USB3_RX_N' and RELOCATED:
     seg(b,n,(target_x,landing_y),(270.0,landing_y),pcbnew.F_Cu); seg(b,n,(270.0,landing_y),d,pcbnew.F_Cu)
    elif suffix == 'CM5_USB3_TX_N' and RELOCATED:
     mid=(170.0,lane_y); seg(b,n,(target_x,landing_y),mid,pcbnew.F_Cu)
     seg(b,n,mid,(mid[0],155.0),pcbnew.F_Cu); seg(b,n,(mid[0],155.0),(220.0,155.0),pcbnew.F_Cu); seg(b,n,(220.0,155.0),(220.0,landing_y),pcbnew.F_Cu); seg(b,n,(220.0,landing_y),d,pcbnew.F_Cu)
    else:
     seg(b,n,(target_x,landing_y),d,pcbnew.F_Cu)
    continue
  if USB_TOP_EAST:
   # Preserve the serialized CM5 source escape, then use four ordered
   # top-side B.Cu corridors and an outboard x>290 approach to U7.  This
   # keeps the USB3 graph outside the SATA island instead of changing the
   # source-side fanout as the rejected USB_EAST trial did.
   first={'CM5_USB3_RX_N':(78.0,103.9),'CM5_USB3_RX_P':(76.0,104.8),
          'CM5_USB3_TX_N':(74.0,108.0),'CM5_USB3_TX_P':(72.0,109.0)}[suffix]
   top={'CM5_USB3_RX_N':(86.0,80.0),'CM5_USB3_RX_P':(84.0,82.0),
        'CM5_USB3_TX_N':(82.0,84.0),'CM5_USB3_TX_P':(80.0,86.0)}[suffix]
   outx={'CM5_USB3_RX_N':295.0,'CM5_USB3_RX_P':296.0,
         'CM5_USB3_TX_N':297.0,'CM5_USB3_TX_P':298.0}[suffix]
   landing={'CM5_USB3_RX_N':(290.0,112.0),'CM5_USB3_RX_P':(291.0,114.5),
            'CM5_USB3_TX_N':(292.0,117.0),'CM5_USB3_TX_P':(293.0,119.5)}[suffix]
   launch=(71.2,s[1]); seg(b,n,s,launch); seg(b,n,launch,first); via(b,n,first)
   seg(b,n,first,top,pcbnew.B_Cu); seg(b,n,top,(outx,top[1]),pcbnew.B_Cu); seg(b,n,(outx,top[1]),(outx,landing[1]),pcbnew.B_Cu); seg(b,n,(outx,landing[1]),landing,pcbnew.B_Cu); via(b,n,landing)
   dog=(d[0],landing[1]-1.0); seg(b,n,landing,dog,pcbnew.F_Cu); seg(b,n,dog,d,pcbnew.F_Cu)
   continue
  if USB_PAIR_SPLIT:
   # Pair-preserving alternative: RX is one B.Cu pair and TX one F.Cu
   # pair.  The two pairs therefore cannot cross in the long corridor;
   # their U7 pad dogbones are kept in separate upper/lower launch bands.
   # Spread the serialized source fanout before the first transition.  The
   # increasing x/y order keeps each vertical escape outside the next
   # source segment instead of placing vias in the adjacent pad launch.
   first={'CM5_USB3_RX_N':(74.0,101.0),'CM5_USB3_RX_P':(84.0,105.0),
          'CM5_USB3_TX_N':(94.0,110.0),'CM5_USB3_TX_P':(104.0,115.0)}[suffix]
   top={'CM5_USB3_RX_N':(74.0,80.0),'CM5_USB3_RX_P':(84.0,82.0),
        'CM5_USB3_TX_N':(94.0,84.0),'CM5_USB3_TX_P':(104.0,86.0)}[suffix]
   # Higher source lane exits use the nearer outboard column so the
   # vertical drops cannot cut across a lower lane's horizontal run.
   outx={'CM5_USB3_RX_N':298.0,'CM5_USB3_RX_P':297.0,
         'CM5_USB3_TX_N':296.0,'CM5_USB3_TX_P':295.0}[suffix]
   landing={'CM5_USB3_RX_N':(300.0,110.0),'CM5_USB3_RX_P':(301.0,112.0),
            'CM5_USB3_TX_N':(302.0,116.0),'CM5_USB3_TX_P':(303.0,118.0)}[suffix]
   launch=(71.2,s[1]); seg(b,n,s,launch); seg(b,n,launch,first)
   via(b,n,first); layer=pcbnew.B_Cu
   seg(b,n,first,(first[0],top[1]),layer); seg(b,n,(first[0],top[1]),(260.0,top[1]),layer)
   seg(b,n,(260.0,top[1]),(outx,top[1]),layer); seg(b,n,(outx,top[1]),(outx,landing[1]),layer); seg(b,n,(outx,landing[1]),landing,pcbnew.B_Cu)
   # Bring every serialized U7 endpoint to an individually separated
   # underside transition, then use only a short F.Cu dogbone into the
   # live SMD pad.  The long layer-separated corridors cannot cut the
   # clock bus or one another.
   via_pos={'CM5_USB3_RX_N':(270.0,120.0),'CM5_USB3_RX_P':(270.5,122.0),
            'CM5_USB3_TX_N':(271.5,124.0),'CM5_USB3_TX_P':(272.0,126.0)}[suffix]
   seg(b,n,landing,via_pos,pcbnew.B_Cu)
   via(b,n,via_pos)
   seg(b,n,via_pos,d,pcbnew.F_Cu)
   continue
  if USB_VERTICAL:
   # Pair-aware vertical-entry experiment: RX approaches the left side of
   # U7 from above on B.Cu, while TX approaches the right side from below
   # on F.Cu.  The long pair corridors are therefore disjoint from the
   # SATA island and from each other.
   first={'CM5_USB3_RX_N':(85.0,103.9),'CM5_USB3_RX_P':(88.0,104.3),
          'CM5_USB3_TX_N':(90.0,106.3),'CM5_USB3_TX_P':(93.0,106.7)}[suffix]
   lane_y={'CM5_USB3_RX_N':80.0,'CM5_USB3_RX_P':82.0,
           'CM5_USB3_TX_N':152.0,'CM5_USB3_TX_P':150.0}[suffix]
   outx={'CM5_USB3_RX_N':295.0,'CM5_USB3_RX_P':296.0,
         'CM5_USB3_TX_N':297.0,'CM5_USB3_TX_P':298.0}[suffix]
   landing={'CM5_USB3_RX_N':(285.0,104.0),'CM5_USB3_RX_P':(286.0,105.0),
            'CM5_USB3_TX_N':(287.0,115.0),'CM5_USB3_TX_P':(288.0,116.0)}[suffix]
   launch=(71.2,s[1]); seg(b,n,s,launch); seg(b,n,launch,first)
   is_rx=suffix.startswith('CM5_USB3_RX_')
   if is_rx: via(b,n,first)
   layer=pcbnew.B_Cu if is_rx else pcbnew.F_Cu
   seg(b,n,first,(first[0],lane_y),layer); seg(b,n,(first[0],lane_y),(outx,lane_y),layer)
   seg(b,n,(outx,lane_y),(outx,landing[1]),layer); seg(b,n,(outx,landing[1]),landing,layer)
   if is_rx: via(b,n,landing)
   seg(b,n,landing,d,pcbnew.F_Cu)
   continue
  if U7ROT == 0 and SKIP_SATA:
   # Rotation-0 diagnostic: U7 USB pads form a vertical side row, so RX
   # enters from the upper B.Cu corridor and TX from the lower F.Cu corridor.
   # This is intentionally USB-only; SATA is regenerated after the USB
   # orientation is proven.
   first={'CM5_USB3_RX_N':(94.0,103.9),'CM5_USB3_RX_P':(90.0,105.5),
          'CM5_USB3_TX_N':(100.0,106.3),'CM5_USB3_TX_P':(96.0,106.7)}[suffix]
   lane_y={'CM5_USB3_RX_N':82.0,'CM5_USB3_RX_P':80.0,
           'CM5_USB3_TX_N':158.0,'CM5_USB3_TX_P':160.0}[suffix]
   outx={'CM5_USB3_RX_N':295.0,'CM5_USB3_RX_P':299.0,
         'CM5_USB3_TX_N':295.0,'CM5_USB3_TX_P':298.0}[suffix]
   landing={'CM5_USB3_RX_N':(294.0,101.0),'CM5_USB3_RX_P':(290.0,103.5),
            'CM5_USB3_TX_N':(297.5,99.0),'CM5_USB3_TX_P':(298.0,98.0)}[suffix]
   launch=(71.2,s[1]); seg(b,n,s,launch); seg(b,n,launch,first)
   is_rx=suffix.startswith('CM5_USB3_RX_')
   if is_rx: via(b,n,first)
   layer=pcbnew.B_Cu if is_rx else pcbnew.F_Cu
   seg(b,n,first,(first[0],lane_y),layer); seg(b,n,(first[0],lane_y),(outx,lane_y),layer)
   seg(b,n,(outx,lane_y),(outx,landing[1]),layer); seg(b,n,(outx,landing[1]),landing,layer)
   if is_rx: via(b,n,landing)
   seg(b,n,landing,d,pcbnew.F_Cu)
   continue
  if U7ROT == 90 and SKIP_SATA:
   # Rotation-90 diagnostic: U7 USB pads form a horizontal top row while
   # SATA remains on the opposite side.  Keep RX and TX on independent
   # long corridors and use one vertical landing per serialized pad x;
   # this avoids fan-in across the pad row.
   first={'CM5_USB3_RX_N':(94.0,103.9),'CM5_USB3_RX_P':(90.0,105.5),
          'CM5_USB3_TX_N':(100.0,106.3),'CM5_USB3_TX_P':(96.0,106.7)}[suffix]
   lane_y={'CM5_USB3_RX_N':82.0,'CM5_USB3_RX_P':80.0,
           'CM5_USB3_TX_N':158.0,'CM5_USB3_TX_P':160.0}[suffix]
   target_x={'CM5_USB3_RX_N':280.0,'CM5_USB3_RX_P':279.5,
             'CM5_USB3_TX_N':278.5,'CM5_USB3_TX_P':278.0}[suffix]
   landing_y={'CM5_USB3_RX_N':98.0,'CM5_USB3_RX_P':96.0,
              'CM5_USB3_TX_N':94.0,'CM5_USB3_TX_P':92.0}[suffix]
   launch=(71.2,s[1]); seg(b,n,s,launch); seg(b,n,launch,first)
   is_rx=suffix.startswith('CM5_USB3_RX_')
   if is_rx: via(b,n,first)
   layer=pcbnew.B_Cu if is_rx else pcbnew.F_Cu
   seg(b,n,first,(first[0],lane_y),layer); seg(b,n,(first[0],lane_y),(292.0,lane_y),layer)
   seg(b,n,(292.0,lane_y),(292.0,landing_y),layer); seg(b,n,(292.0,landing_y),(target_x,landing_y),layer)
   if is_rx: via(b,n,(target_x,landing_y))
   seg(b,n,(target_x,landing_y),d,pcbnew.F_Cu)
   continue
  if U7ROT == 180 and SKIP_SATA:
   # Rotation-180 diagnostic: mirrored vertical USB side row.  Use distinct
   # upper/lower pair corridors and serialized pad coordinates so the final
   # approach is monotonic rather than a four-lane fan-in.
   first={'CM5_USB3_RX_N':(94.0,103.9),'CM5_USB3_RX_P':(90.0,105.5),
          'CM5_USB3_TX_N':(100.0,106.3),'CM5_USB3_TX_P':(96.0,106.7)}[suffix]
   lane_y={'CM5_USB3_RX_N':82.0,'CM5_USB3_RX_P':80.0,
           'CM5_USB3_TX_N':158.0,'CM5_USB3_TX_P':160.0}[suffix]
   target_x={'CM5_USB3_RX_N':275.5,'CM5_USB3_RX_P':275.5,
             'CM5_USB3_TX_N':275.5,'CM5_USB3_TX_P':275.5}[suffix]
   target_y={'CM5_USB3_RX_N':105.0,'CM5_USB3_RX_P':105.5,
             'CM5_USB3_TX_N':106.5,'CM5_USB3_TX_P':107.0}[suffix]
   landing_x={'CM5_USB3_RX_N':272.0,'CM5_USB3_RX_P':270.0,
              'CM5_USB3_TX_N':268.0,'CM5_USB3_TX_P':266.0}[suffix]
   launch=(71.2,s[1]); seg(b,n,s,launch); seg(b,n,launch,first)
   is_rx=suffix.startswith('CM5_USB3_RX_')
   if is_rx: via(b,n,first)
   layer=pcbnew.B_Cu if is_rx else pcbnew.F_Cu
   seg(b,n,first,(first[0],lane_y),layer); seg(b,n,(first[0],lane_y),(landing_x,lane_y),layer)
   seg(b,n,(landing_x,lane_y),(landing_x,target_y),layer); seg(b,n,(landing_x,target_y),(target_x,target_y),layer)
   if is_rx: via(b,n,(target_x,target_y))
   seg(b,n,(target_x,target_y),d,pcbnew.F_Cu)
   continue
  seg(b,n,s,(start[0],s[1])); seg(b,n,(start[0],s[1]),start); via(b,n,start); seg(b,n,start,far,pcbnew.B_Cu)
  # The rotated U7 USB pads share a continuous bottom row.  Do not run a
  # same-layer horizontal track through that row; use a distinct B.Cu lane
  # and one ordinary via directly below each live destination pad.
  _i=['CM5_USB3_RX_N','CM5_USB3_RX_P','CM5_USB3_TX_N','CM5_USB3_TX_P'].index(suffix)
  landing=([(286.0,112.0),(287.5,114.5),(289.0,117.0),(290.5,119.5)][_i] if USB_EAST else [(276.0,112.0),(277.5,114.5),(280.0,117.0),(285.5,119.5)][_i])
  seg(b,n,far,landing,pcbnew.B_Cu); via(b,n,landing)
  dog=(d[0],landing[1]-1.0); seg(b,n,landing,dog,pcbnew.F_Cu); seg(b,n,dog,d,pcbnew.F_Cu)
 # SATA split capacitors.  Pair lanes are layer-separated after live pad
 # escapes; each transition is outside an SMD pad field.
 sata=(('BRIDGE_SATA_TX_P','57','1','C30',pcbnew.F_Cu,(224,96)),
       ('BRIDGE_SATA_TX_N','56','2','C31',pcbnew.B_Cu,(223,99)),
       ('BRIDGE_SATA_RX_P','60','3','C32',pcbnew.F_Cu,(216,103)),
       ('BRIDGE_SATA_RX_N','59','4','C33',pcbnew.B_Cu,(217,105)))
 for bn,upn,jn,cr,layer,esc in sata:
  if SKIP_SATA or CLOCK_ONLY:
   continue
  bridge=N['/STORAGE/'+bn]; socket=N['/STORAGE/'+bn.replace('BRIDGE_SATA_','SATA_M2_')]
  cp={str(p.GetNumber()):pos(p) for p in caps[cr].Pads()}; a=U[upn]; z=J[jn]
  setpad(pad(caps[cr],'1'),socket); setpad(pad(caps[cr],'2'),bridge); setpad(pad(j,jn),socket); setpad(pad(u,upn),bridge)
  if SATA270:
   L=lambda x,y:(x+(U7X-280.0),y+(U7Y-105.0))
   # Never start a B.Cu segment directly on an SMD pad.  Use a short
   # F.Cu dogbone and an ordinary through-via outside the capacitor pad.
   cap_via = (cp['2'][0]+1.0, cp['2'][1])
   if bn in ('BRIDGE_SATA_TX_P','BRIDGE_SATA_RX_P'):
    if bn == 'BRIDGE_SATA_RX_P':
     e=(a[0]+3.0,a[1]); seg(b,bridge,a,e,pcbnew.F_Cu); via(b,bridge,e); seg(b,bridge,e,cap_via,pcbnew.B_Cu); via(b,bridge,cap_via); seg(b,bridge,cap_via,cp['2'],pcbnew.F_Cu)
    else:
     seg(b,bridge,a,cp['2'],pcbnew.F_Cu)
   else:
    if bn == 'BRIDGE_SATA_RX_N':
     seg(b,bridge,a,cp['2'],pcbnew.F_Cu)
    else:
     e=(a[0]-3.0,a[1])
     seg(b,bridge,a,e,pcbnew.F_Cu); via(b,bridge,e); seg(b,bridge,e,cap_via,pcbnew.B_Cu); via(b,bridge,cap_via); seg(b,bridge,cap_via,cp['2'],pcbnew.F_Cu)
   # Keep each SATA pair on one signal layer.  The positive lane uses the
   # right-hand corridor and the negative lane the left-hand corridor; the
   # two pairs are assigned to opposite layers so the alternating M.2 pad
   # columns do not force a same-layer crossing.
   if bn == 'BRIDGE_SATA_TX_P':
    p=L(235.0,110.0); seg(b,socket,cp['1'],p,pcbnew.F_Cu); seg(b,socket,p,L(235.0,129.0),pcbnew.F_Cu); seg(b,socket,L(235.0,129.0),L(208.0,129.0),pcbnew.F_Cu); seg(b,socket,L(208.0,129.0),L(208.0,130.75),pcbnew.F_Cu); seg(b,socket,L(208.0,130.75),z,pcbnew.F_Cu)
   elif bn == 'BRIDGE_SATA_TX_N':
    p=L(190.0,108.0); seg(b,socket,cp['1'],p,pcbnew.F_Cu); seg(b,socket,p,L(190.0,131.0),pcbnew.F_Cu); seg(b,socket,L(190.0,131.0),z,pcbnew.F_Cu)
   elif bn == 'BRIDGE_SATA_RX_P':
    p=L(238.5,cp['1'][1]); seg(b,socket,cp['1'],p,pcbnew.F_Cu); via(b,socket,p); m=L(215.0,p[1]); seg(b,socket,p,m,pcbnew.B_Cu); q=L(215.0,131.25); seg(b,socket,m,q,pcbnew.B_Cu); via(b,socket,q); seg(b,socket,q,z,pcbnew.F_Cu)
   else:
    p=L(238.5,cp['1'][1]); seg(b,socket,cp['1'],p,pcbnew.F_Cu); via(b,socket,p); m=L(210.0,p[1]); seg(b,socket,p,m,pcbnew.B_Cu); q=L(210.0,132.5); seg(b,socket,m,q,pcbnew.B_Cu); r=L(190.0,132.5); seg(b,socket,q,r,pcbnew.B_Cu); via(b,socket,r); seg(b,socket,r,L(190.0,131.5),pcbnew.F_Cu); seg(b,socket,L(190.0,131.5),z,pcbnew.F_Cu)
   continue
  if u.GetOrientationDegrees() == -90.0 and j.GetOrientationDegrees() == 90.0:
   L=lambda x,y:(x+(U7X-280.0),y+(U7Y-105.0))
   # Rot270 U7 exposes SATA on a single west-facing row.  Use live pad
   # coordinates and a pair-per-layer monotonic launch to the left-column
   # M.2 pads; the two pairs never share a signal layer.
   if bn == 'BRIDGE_SATA_TX_P':
    e=(a[0]-3,a[1]); seg(b,bridge,a,e); seg(b,bridge,e,cp['2'])
   elif bn == 'BRIDGE_SATA_TX_N':
    e=(a[0]-2,a[1]-1.0); via(b,bridge,e); seg(b,bridge,a,e); seg(b,bridge,e,cp['2'],pcbnew.B_Cu)
   elif bn == 'BRIDGE_SATA_RX_P':
    e=(a[0]-5,a[1]+2.0); via(b,bridge,e); seg(b,bridge,a,e); seg(b,bridge,e,cp['2'],pcbnew.B_Cu)
   else:
    e=(a[0]-4,a[1]+4.0); via(b,bridge,e); seg(b,bridge,a,e); seg(b,bridge,e,cp['2'],pcbnew.B_Cu)
   # Legal horizontal M.2 orientation: independent live lanes approach the
   # rotated socket from four disjoint corridors around U7.
   if bn == 'BRIDGE_SATA_TX_P':
    q=L(235.0,96.0); seg(b,socket,cp['1'],q,pcbnew.F_Cu); r=L(215.0,96.0); seg(b,socket,q,r,pcbnew.F_Cu); seg(b,socket,r,(r[0],d[1]),pcbnew.F_Cu); seg(b,socket,(r[0],d[1]),d)
   elif bn == 'BRIDGE_SATA_TX_N':
    q=L(235.0,100.0); seg(b,socket,cp['1'],q,pcbnew.F_Cu); via(b,socket,q); r=L(210.0,100.0); seg(b,socket,q,r,pcbnew.B_Cu); via(b,socket,r); seg(b,socket,r,(r[0],d[1]+6),pcbnew.B_Cu); via(b,socket,(r[0],d[1]+6)); seg(b,socket,(r[0],d[1]+6),d)
   elif bn == 'BRIDGE_SATA_RX_P':
    q=L(235.0,108.0); seg(b,socket,cp['1'],q,pcbnew.F_Cu); via(b,socket,q); r=L(205.0,108.0); seg(b,socket,q,r,pcbnew.B_Cu); via(b,socket,r); seg(b,socket,r,(r[0],d[1]-5),pcbnew.B_Cu); via(b,socket,(r[0],d[1]-5)); seg(b,socket,(r[0],d[1]-5),d)
   else:
    q=L(235.0,112.0); seg(b,socket,cp['1'],q,pcbnew.F_Cu); via(b,socket,q); r=L(215.0,112.0); seg(b,socket,q,r,pcbnew.B_Cu); via(b,socket,r); seg(b,socket,r,(r[0],d[1]+10),pcbnew.B_Cu); via(b,socket,(r[0],d[1]+10)); seg(b,socket,(r[0],d[1]+10),d)
  elif layer==pcbnew.F_Cu:
   seg(b,bridge,a,(a[0]-2,a[1])); seg(b,bridge,(a[0]-2,a[1]),cp['2'])
   seg(b,socket,cp['1'],(230,cp['1'][1])); seg(b,socket,(230,cp['1'][1]),(230,z[1])); seg(b,socket,(230,z[1]),z)
  else:
   e=(a[0]-3,a[1]); via(b,bridge,e); seg(b,bridge,a,e,pcbnew.F_Cu); seg(b,bridge,e,cp['2'],pcbnew.B_Cu)
   e2=(232,cp['1'][1]); via(b,socket,e2); seg(b,socket,cp['1'],e2,pcbnew.F_Cu); seg(b,socket,e2,(232,z[1]),pcbnew.B_Cu); via(b,socket,(232,z[1])); seg(b,socket,(232,z[1]),z)
 # Clock net assignments and live endpoint routes.  VSSOSC is a private
 # return with ordinary through-vias beside the low-profile support parts.
 if SKIP_CLOCK:
  b.Save(str(OUT)); print(OUT); return
 maps={'Y1':{'1':'/STORAGE/BRIDGE_XI','2':'/STORAGE/BRIDGE_VSSOSC','3':'/STORAGE/BRIDGE_XO','4':'/STORAGE/BRIDGE_VSSOSC'},
       'R23':{'1':'/STORAGE/BRIDGE_XI','2':'/STORAGE/BRIDGE_XO'},'C42':{'1':'/STORAGE/BRIDGE_XI','2':'/STORAGE/BRIDGE_VSSOSC'},'C43':{'1':'/STORAGE/BRIDGE_XO','2':'/STORAGE/BRIDGE_VSSOSC'}}
 for ref,m in maps.items():
  for p in b.FindFootprintByReference(ref).Pads(): setpad(p,N[m[str(p.GetNumber())]])
 for pn,nm in (('52','/STORAGE/BRIDGE_XI'),('53','/STORAGE/BRIDGE_VSSOSC'),('54','/STORAGE/BRIDGE_XO')): setpad(pad(u,pn),N[nm])
 Y={str(p.GetNumber()):pos(p) for p in b.FindFootprintByReference('Y1').Pads()}; R23={str(p.GetNumber()):pos(p) for p in b.FindFootprintByReference('R23').Pads()}; C42={str(p.GetNumber()):pos(p) for p in b.FindFootprintByReference('C42').Pads()}; C43={str(p.GetNumber()):pos(p) for p in b.FindFootprintByReference('C43').Pads()}
 xi,xo,vs=N['/STORAGE/BRIDGE_XI'],N['/STORAGE/BRIDGE_XO'],N['/STORAGE/BRIDGE_VSSOSC']
 # Clock island: separated north-acreage lanes, with live pad endpoints.
 y1x,y1y=pos(b.FindFootprintByReference('Y1').Pads()[0]); r1x,r1y=R23['1']; r2x,r2y=R23['2']
 xi_bus=(r1x,y1y-9.0); xi_e=(U['52'][0]-5.5,U['52'][1]); seg(b,xi,U['52'],xi_e); seg(b,xi,xi_e,(xi_e[0],xi_bus[1])); seg(b,xi,(xi_e[0],xi_bus[1]),xi_bus); seg(b,xi,xi_bus,R23['1']); seg(b,xi,C42['1'],(C42['1'][0],xi_bus[1])); seg(b,xi,(C42['1'][0],xi_bus[1]),xi_bus); seg(b,xi,Y['1'],(Y['1'][0],xi_bus[1])); seg(b,xi,(Y['1'][0],xi_bus[1]),xi_bus)
 xo_e=(U['54'][0]-9.5,U['54'][1]); xo_bus=(C43['1'][0],y1y+7.0); seg(b,xo,U['54'],xo_e); seg(b,xo,xo_e,(xo_e[0],xo_bus[1])); seg(b,xo,(xo_e[0],xo_bus[1]),xo_bus); seg(b,xo,xo_bus,C43['1']); seg(b,xo,C43['1'],R23['2']); xo_y3=(Y['3'][0],y1y+4.0); seg(b,xo,Y['3'],xo_y3); seg(b,xo,xo_y3,(C43['1'][0],xo_y3[1])); seg(b,xo,(C43['1'][0],xo_y3[1]),C43['1'])
 vs_e=(U['53'][0]-7.5,U['53'][1]); vs_bus=(C43['2'][0]+3.0,y1y+12.0); seg(b,vs,U['53'],vs_e); seg(b,vs,vs_e,(vs_e[0],vs_bus[1])); via_sig(b,vs,(vs_e[0],vs_bus[1])); seg(b,vs,(vs_e[0],vs_bus[1]),vs_bus,pcbnew.B_Cu)
 # Each support return uses a short pad dogbone to its own B.Cu via; the
 # shared return bus is below the support field and cannot cross XO/XI.
 yv=vs_bus[1]
 for p,q in ((Y['2'],(Y['2'][0]-4.0,yv)),(Y['4'],(Y['4'][0]+4.4,yv)),(C42['2'],(C42['2'][0],C42['2'][1]+2.0)),(C43['2'],(C43['2'][0]-5.0,yv))):
  if p == Y['4'] or p == C43['2']:
   # These two pads sit beside the XO support lane. Escape on F.Cu only to
   # an offset via, then stay on B.Cu through the return bus.
   e=(p[0],p[1]-3.0); seg(b,vs,p,e); via_sig(b,vs,e); seg(b,vs,e,q,pcbnew.B_Cu)
  elif p == C43['2']:
   mid=(p[0],p[1]-3.0); seg(b,vs,p,mid); seg(b,vs,mid,(q[0],mid[1])); seg(b,vs,(q[0],mid[1]),q)
  elif q[1] == yv:
   seg(b,vs,p,(q[0],p[1])); seg(b,vs,(q[0],p[1]),q)
  else: seg(b,vs,p,q)
  if p != Y['4'] and p != C43['2']: via_sig(b,vs,q)
  if q[1] != yv: seg(b,vs,q,(q[0],yv),pcbnew.B_Cu)
  seg(b,vs,(q[0],yv),vs_bus,pcbnew.B_Cu)
 # FREQSEL0/1 and VDDIO high on the local 3V3 net; local short fanout.
 v33=b.FindNet('/STORAGE/BRIDGE_3V3')
 for pn in ('24','30','31'): setpad(pad(u,pn),v33)
 seg(b,v33,U['24'],(287,106)); seg(b,v33,(287,106),U['30']); seg(b,v33,(287,106),U['31'])
 b.Save(str(OUT))
 # Remove only known donor duplicate net fields from U7 pads 5-12 in the
 # serialized footprint; this is the same deterministic cleanup used by the
 # coordinated authoring path.
 text=Path(OUT).read_text(); us=text.index('(footprint "TUSB9261IPVP_HTQFP64"'); ue=text.index('\n\t(footprint ',us+1); utext=text[us:ue]
 for pn in range(5,13):
  m=re.search(r'(?ms)(\n\t\t\(pad "'+str(pn)+r'".*?)(?=\n\t\t\(pad |\n\t\))',utext)
  if m: utext=utext[:m.start(1)]+re.sub(r'\n\t\t\t\(net "[^"]*"\)','',m.group(1))+utext[m.end(1):]
 Path(OUT).write_text(text[:us]+utext+text[ue:]); print(OUT)
if __name__=='__main__': main()
